charcole/zmachine3270/Firmware/main/libssh2/kex.c

/* Copyright (c) 2004-2007, Sara Golemon <sarag@libssh2.org>
 * Copyright (c) 2010-2019, Daniel Stenberg <daniel@haxx.se>
 * All rights reserved.
 *
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
 *   Redistributions of source code must retain the above
 *   copyright notice, this list of conditions and the
 *   following disclaimer.
 *
 *   Redistributions in binary form must reproduce the above
 *   copyright notice, this list of conditions and the following
 *   disclaimer in the documentation and/or other materials
 *   provided with the distribution.
 *
 *   Neither the name of the copyright holder nor the names
 *   of any other contributors may be used to endorse or
 *   promote products derived from this software without
 *   specific prior written permission.
 *
 * THIS SOFTWARE IS PROVIDED BY THE COPYRIGHT HOLDERS AND
 * CONTRIBUTORS "AS IS" AND ANY EXPRESS OR IMPLIED WARRANTIES,
 * INCLUDING, BUT NOT LIMITED TO, THE IMPLIED WARRANTIES
 * OF MERCHANTABILITY AND FITNESS FOR A PARTICULAR PURPOSE
 * ARE DISCLAIMED. IN NO EVENT SHALL THE COPYRIGHT OWNER OR
 * CONTRIBUTORS BE LIABLE FOR ANY DIRECT, INDIRECT, INCIDENTAL,
 * SPECIAL, EXEMPLARY, OR CONSEQUENTIAL DAMAGES (INCLUDING,
 * BUT NOT LIMITED TO, PROCUREMENT OF SUBSTITUTE GOODS OR
 * SERVICES; LOSS OF USE, DATA, OR PROFITS; OR BUSINESS
 * INTERRUPTION) HOWEVER CAUSED AND ON ANY THEORY OF LIABILITY,
 * WHETHER IN CONTRACT, STRICT LIABILITY, OR TORT (INCLUDING
 * NEGLIGENCE OR OTHERWISE) ARISING IN ANY WAY OUT OF THE
 * USE OF THIS SOFTWARE, EVEN IF ADVISED OF THE POSSIBILITY
 * OF SUCH DAMAGE.
 */

#include "libssh2_priv.h"

#include "transport.h"
#include "comp.h"
#include "mac.h"

/* TODO: Switch this to an inline and handle alloc() failures */
/* Helper macro called from
   kex_method_diffie_hellman_group1_sha1_key_exchange */
#define LIBSSH2_KEX_METHOD_DIFFIE_HELLMAN_SHA1_HASH(value, reqlen, version) \
    {                                                                   \
        libssh2_sha1_ctx hash;                                          \
        unsigned long len = 0;                                          \
        if(!(value)) {                                                  \
            value = LIBSSH2_ALLOC(session, reqlen + SHA_DIGEST_LENGTH); \
        }                                                               \
        if(value)                                                       \
            while(len < (unsigned long)reqlen) {                        \
                libssh2_sha1_init(&hash);                               \
                libssh2_sha1_update(hash, exchange_state->k_value,      \
                                    exchange_state->k_value_len);       \
                libssh2_sha1_update(hash, exchange_state->h_sig_comp,   \
                                    SHA_DIGEST_LENGTH);                 \
                if(len > 0) {                                           \
                    libssh2_sha1_update(hash, value, len);              \
                }                                                       \
                else {                                                  \
                    libssh2_sha1_update(hash, (version), 1);            \
                    libssh2_sha1_update(hash, session->session_id,      \
                                        session->session_id_len);       \
                }                                                       \
                libssh2_sha1_final(hash, (value) + len);                \
                len += SHA_DIGEST_LENGTH;                               \
            }                                                           \
    }                                                                   \


#define LIBSSH2_KEX_METHOD_EC_SHA_VALUE_HASH(value, reqlen, version)    \
    {                                                                   \
        if(type == LIBSSH2_EC_CURVE_NISTP256) {                         \
            LIBSSH2_KEX_METHOD_SHA_VALUE_HASH(256, value, reqlen, version); \
        }                                                               \
        else if(type == LIBSSH2_EC_CURVE_NISTP384) {                    \
            LIBSSH2_KEX_METHOD_SHA_VALUE_HASH(384, value, reqlen, version); \
        }                                                               \
        else if(type == LIBSSH2_EC_CURVE_NISTP521) {                    \
            LIBSSH2_KEX_METHOD_SHA_VALUE_HASH(512, value, reqlen, version); \
        }                                                               \
    }                                                                   \


#define LIBSSH2_KEX_METHOD_SHA_VALUE_HASH(digest_type, value,           \
                                          reqlen, version)              \
{                                                                       \
    libssh2_sha##digest_type##_ctx hash;                                \
    unsigned long len = 0;                                              \
    if(!(value)) {                                                      \
        value = LIBSSH2_ALLOC(session,                                  \
                              reqlen + SHA##digest_type##_DIGEST_LENGTH); \
    }                                                                   \
    if(value)                                                           \
        while(len < (unsigned long)reqlen) {                            \
            libssh2_sha##digest_type##_init(&hash);                     \
            libssh2_sha##digest_type##_update(hash,                     \
                                              exchange_state->k_value,  \
                                              exchange_state->k_value_len); \
            libssh2_sha##digest_type##_update(hash,                     \
                                              exchange_state->h_sig_comp, \
                                         SHA##digest_type##_DIGEST_LENGTH); \
            if(len > 0) {                                               \
                libssh2_sha##digest_type##_update(hash, value, len);    \
            }                                                           \
            else {                                                      \
                libssh2_sha##digest_type##_update(hash, (version), 1);  \
                libssh2_sha##digest_type##_update(hash, session->session_id, \
                                                  session->session_id_len); \
            }                                                           \
            libssh2_sha##digest_type##_final(hash, (value) + len);      \
            len += SHA##digest_type##_DIGEST_LENGTH;                    \
        }                                                               \
}


/*
 * diffie_hellman_sha1
 *
 * Diffie Hellman Key Exchange, Group Agnostic
 */
static int diffie_hellman_sha1(LIBSSH2_SESSION *session,
                               _libssh2_bn *g,
                               _libssh2_bn *p,
                               int group_order,
                               unsigned char packet_type_init,
                               unsigned char packet_type_reply,
                               unsigned char *midhash,
                               unsigned long midhash_len,
                               kmdhgGPshakex_state_t *exchange_state)
{
    int ret = 0;
    int rc;
    libssh2_sha1_ctx exchange_hash_ctx;

    if(exchange_state->state == libssh2_NB_state_idle) {
        /* Setup initial values */
        exchange_state->e_packet = NULL;
        exchange_state->s_packet = NULL;
        exchange_state->k_value = NULL;
        exchange_state->ctx = _libssh2_bn_ctx_new();
        libssh2_dh_init(&exchange_state->x);
        exchange_state->e = _libssh2_bn_init(); /* g^x mod p */
        exchange_state->f = _libssh2_bn_init_from_bin(); /* g^(Random from
                                                            server) mod p */
        exchange_state->k = _libssh2_bn_init(); /* The shared secret: f^x mod
                                                   p */

        /* Zero the whole thing out */
        memset(&exchange_state->req_state, 0, sizeof(packet_require_state_t));

        /* Generate x and e */
        rc = libssh2_dh_key_pair(&exchange_state->x, exchange_state->e, g, p,
                                 group_order, exchange_state->ctx);
        if(rc)
            goto clean_exit;

        /* Send KEX init */
        /* packet_type(1) + String Length(4) + leading 0(1) */
        exchange_state->e_packet_len =
            _libssh2_bn_bytes(exchange_state->e) + 6;
        if(_libssh2_bn_bits(exchange_state->e) % 8) {
            /* Leading 00 not needed */
            exchange_state->e_packet_len--;
        }

        exchange_state->e_packet =
            LIBSSH2_ALLOC(session, exchange_state->e_packet_len);
        if(!exchange_state->e_packet) {
            ret = _libssh2_error(session, LIBSSH2_ERROR_ALLOC,
                                 "Out of memory error");
            goto clean_exit;
        }
        exchange_state->e_packet[0] = packet_type_init;
        _libssh2_htonu32(exchange_state->e_packet + 1,
                         exchange_state->e_packet_len - 5);
        if(_libssh2_bn_bits(exchange_state->e) % 8) {
            _libssh2_bn_to_bin(exchange_state->e,
                               exchange_state->e_packet + 5);
        }
        else {
            exchange_state->e_packet[5] = 0;
            _libssh2_bn_to_bin(exchange_state->e,
                               exchange_state->e_packet + 6);
        }

        _libssh2_debug(session, LIBSSH2_TRACE_KEX, "Sending KEX packet %d",
                       (int) packet_type_init);
        exchange_state->state = libssh2_NB_state_created;
    }

    if(exchange_state->state == libssh2_NB_state_created) {
        rc = _libssh2_transport_send(session, exchange_state->e_packet,
                                     exchange_state->e_packet_len,
                                     NULL, 0);
        if(rc == LIBSSH2_ERROR_EAGAIN) {
            return rc;
        }
        else if(rc) {
            ret = _libssh2_error(session, rc,
                                 "Unable to send KEX init message");
            goto clean_exit;
        }
        exchange_state->state = libssh2_NB_state_sent;
    }

    if(exchange_state->state == libssh2_NB_state_sent) {
        if(session->burn_optimistic_kexinit) {
            /* The first KEX packet to come along will be the guess initially
             * sent by the server.  That guess turned out to be wrong so we
             * need to silently ignore it */
            int burn_type;

            _libssh2_debug(session, LIBSSH2_TRACE_KEX,
                           "Waiting for badly guessed KEX packet "
                           "(to be ignored)");
            burn_type =
                _libssh2_packet_burn(session, &exchange_state->burn_state);
            if(burn_type == LIBSSH2_ERROR_EAGAIN) {
                return burn_type;
            }
            else if(burn_type <= 0) {
                /* Failed to receive a packet */
                ret = burn_type;
                goto clean_exit;
            }
            session->burn_optimistic_kexinit = 0;

            _libssh2_debug(session, LIBSSH2_TRACE_KEX,
                           "Burnt packet of type: %02x",
                           (unsigned int) burn_type);
        }

        exchange_state->state = libssh2_NB_state_sent1;
    }

    if(exchange_state->state == libssh2_NB_state_sent1) {
        /* Wait for KEX reply */
        struct string_buf buf;
        size_t host_key_len;

        rc = _libssh2_packet_require(session, packet_type_reply,
                                     &exchange_state->s_packet,
                                     &exchange_state->s_packet_len, 0, NULL,
                                     0, &exchange_state->req_state);
        if(rc == LIBSSH2_ERROR_EAGAIN) {
            return rc;
        }
        if(rc) {
            ret = _libssh2_error(session, LIBSSH2_ERROR_TIMEOUT,
                                 "Timed out waiting for KEX reply");
            goto clean_exit;
        }

        /* Parse KEXDH_REPLY */
        if(exchange_state->s_packet_len < 5) {
            ret = _libssh2_error(session, LIBSSH2_ERROR_PROTO,
                                 "Unexpected packet length");
            goto clean_exit;
        }

        buf.data = exchange_state->s_packet;
        buf.len = exchange_state->s_packet_len;
        buf.dataptr = buf.data;
        buf.dataptr++; /* advance past type */

        if(session->server_hostkey)
            LIBSSH2_FREE(session, session->server_hostkey);

        if(_libssh2_copy_string(session, &buf, &(session->server_hostkey),
                                &host_key_len)) {
            ret = _libssh2_error(session, LIBSSH2_ERROR_ALLOC,
                                 "Could not copy host key");
            goto clean_exit;
        }

        session->server_hostkey_len = (uint32_t)host_key_len;

#if LIBSSH2_MD5
        {
            libssh2_md5_ctx fingerprint_ctx;

            if(libssh2_md5_init(&fingerprint_ctx)) {
                libssh2_md5_update(fingerprint_ctx, session->server_hostkey,
                                   session->server_hostkey_len);
                libssh2_md5_final(fingerprint_ctx,
                                  session->server_hostkey_md5);
                session->server_hostkey_md5_valid = TRUE;
            }
            else {
                session->server_hostkey_md5_valid = FALSE;
            }
        }
#ifdef LIBSSH2DEBUG
        {
            char fingerprint[50], *fprint = fingerprint;
            int i;
            for(i = 0; i < 16; i++, fprint += 3) {
                snprintf(fprint, 4, "%02x:", session->server_hostkey_md5[i]);
            }
            *(--fprint) = '\0';
            _libssh2_debug(session, LIBSSH2_TRACE_KEX,
                           "Server's MD5 Fingerprint: %s", fingerprint);
        }
#endif /* LIBSSH2DEBUG */
#endif /* ! LIBSSH2_MD5 */

        {
            libssh2_sha1_ctx fingerprint_ctx;

            if(libssh2_sha1_init(&fingerprint_ctx)) {
                libssh2_sha1_update(fingerprint_ctx, session->server_hostkey,
                                    session->server_hostkey_len);
                libssh2_sha1_final(fingerprint_ctx,
                                   session->server_hostkey_sha1);
                session->server_hostkey_sha1_valid = TRUE;
            }
            else {
                session->server_hostkey_sha1_valid = FALSE;
            }
        }
#ifdef LIBSSH2DEBUG
        {
            char fingerprint[64], *fprint = fingerprint;
            int i;

            for(i = 0; i < 20; i++, fprint += 3) {
                snprintf(fprint, 4, "%02x:", session->server_hostkey_sha1[i]);
            }
            *(--fprint) = '\0';
            _libssh2_debug(session, LIBSSH2_TRACE_KEX,
                           "Server's SHA1 Fingerprint: %s", fingerprint);
        }
#endif /* LIBSSH2DEBUG */

        {
            libssh2_sha256_ctx fingerprint_ctx;

            if(libssh2_sha256_init(&fingerprint_ctx)) {
                libssh2_sha256_update(fingerprint_ctx, session->server_hostkey,
                                    session->server_hostkey_len);
                libssh2_sha256_final(fingerprint_ctx,
                                   session->server_hostkey_sha256);
                session->server_hostkey_sha256_valid = TRUE;
            }
            else {
                session->server_hostkey_sha256_valid = FALSE;
            }
        }
#ifdef LIBSSH2DEBUG
        {
            char *base64Fingerprint = NULL;
            _libssh2_base64_encode(session,
                                   (const char *)
                                   session->server_hostkey_sha256,
                                   SHA256_DIGEST_LENGTH, &base64Fingerprint);
            if(base64Fingerprint != NULL) {
                _libssh2_debug(session, LIBSSH2_TRACE_KEX,
                               "Server's SHA256 Fingerprint: %s",
                               base64Fingerprint);
                LIBSSH2_FREE(session, base64Fingerprint);
            }
        }
#endif /* LIBSSH2DEBUG */


        if(session->hostkey->init(session, session->server_hostkey,
                                   session->server_hostkey_len,
                                   &session->server_hostkey_abstract)) {
            ret = _libssh2_error(session, LIBSSH2_ERROR_HOSTKEY_INIT,
                                 "Unable to initialize hostkey importer");
            goto clean_exit;
        }

        if(_libssh2_get_string(&buf, &(exchange_state->f_value),
                               &(exchange_state->f_value_len))) {
            ret = _libssh2_error(session, LIBSSH2_ERROR_HOSTKEY_INIT,
                                 "Unable to get f value");
            goto clean_exit;
        }

        _libssh2_bn_from_bin(exchange_state->f, exchange_state->f_value_len,
                             exchange_state->f_value);

        if(_libssh2_get_string(&buf, &(exchange_state->h_sig),
                               &(exchange_state->h_sig_len))) {
            ret = _libssh2_error(session, LIBSSH2_ERROR_HOSTKEY_INIT,
                                 "Unable to get h sig");
            goto clean_exit;
        }

        /* Compute the shared secret */
        libssh2_dh_secret(&exchange_state->x, exchange_state->k,
                          exchange_state->f, p, exchange_state->ctx);
        exchange_state->k_value_len = _libssh2_bn_bytes(exchange_state->k) + 5;
        if(_libssh2_bn_bits(exchange_state->k) % 8) {
            /* don't need leading 00 */
            exchange_state->k_value_len--;
        }
        exchange_state->k_value =
            LIBSSH2_ALLOC(session, exchange_state->k_value_len);
        if(!exchange_state->k_value) {
            ret = _libssh2_error(session, LIBSSH2_ERROR_ALLOC,
                                 "Unable to allocate buffer for K");
            goto clean_exit;
        }
        _libssh2_htonu32(exchange_state->k_value,
                         exchange_state->k_value_len - 4);
        if(_libssh2_bn_bits(exchange_state->k) % 8) {
            _libssh2_bn_to_bin(exchange_state->k, exchange_state->k_value + 4);
        }
        else {
            exchange_state->k_value[4] = 0;
            _libssh2_bn_to_bin(exchange_state->k, exchange_state->k_value + 5);
        }

        exchange_state->exchange_hash = (void *)&exchange_hash_ctx;
        libssh2_sha1_init(&exchange_hash_ctx);

        if(session->local.banner) {
            _libssh2_htonu32(exchange_state->h_sig_comp,
                             strlen((char *) session->local.banner) - 2);
            libssh2_sha1_update(exchange_hash_ctx,
                                exchange_state->h_sig_comp, 4);
            libssh2_sha1_update(exchange_hash_ctx,
                                session->local.banner,
                                strlen((char *) session->local.banner) - 2);
        }
        else {
            _libssh2_htonu32(exchange_state->h_sig_comp,
                             sizeof(LIBSSH2_SSH_DEFAULT_BANNER) - 1);
            libssh2_sha1_update(exchange_hash_ctx,
                                exchange_state->h_sig_comp, 4);
            libssh2_sha1_update(exchange_hash_ctx,
                                (const unsigned char *)
                                LIBSSH2_SSH_DEFAULT_BANNER,
                                sizeof(LIBSSH2_SSH_DEFAULT_BANNER) - 1);
        }

        _libssh2_htonu32(exchange_state->h_sig_comp,
                         strlen((char *) session->remote.banner));
        libssh2_sha1_update(exchange_hash_ctx,
                            exchange_state->h_sig_comp, 4);
        libssh2_sha1_update(exchange_hash_ctx,
                            session->remote.banner,
                            strlen((char *) session->remote.banner));

        _libssh2_htonu32(exchange_state->h_sig_comp,
                         session->local.kexinit_len);
        libssh2_sha1_update(exchange_hash_ctx,
                            exchange_state->h_sig_comp, 4);
        libssh2_sha1_update(exchange_hash_ctx,
                            session->local.kexinit,
                            session->local.kexinit_len);

        _libssh2_htonu32(exchange_state->h_sig_comp,
                         session->remote.kexinit_len);
        libssh2_sha1_update(exchange_hash_ctx,
                            exchange_state->h_sig_comp, 4);
        libssh2_sha1_update(exchange_hash_ctx,
                            session->remote.kexinit,
                            session->remote.kexinit_len);

        _libssh2_htonu32(exchange_state->h_sig_comp,
                         session->server_hostkey_len);
        libssh2_sha1_update(exchange_hash_ctx,
                            exchange_state->h_sig_comp, 4);
        libssh2_sha1_update(exchange_hash_ctx,
                            session->server_hostkey,
                            session->server_hostkey_len);

        if(packet_type_init == SSH_MSG_KEX_DH_GEX_INIT) {
            /* diffie-hellman-group-exchange hashes additional fields */
#ifdef LIBSSH2_DH_GEX_NEW
            _libssh2_htonu32(exchange_state->h_sig_comp,
                             LIBSSH2_DH_GEX_MINGROUP);
            _libssh2_htonu32(exchange_state->h_sig_comp + 4,
                             LIBSSH2_DH_GEX_OPTGROUP);
            _libssh2_htonu32(exchange_state->h_sig_comp + 8,
                             LIBSSH2_DH_GEX_MAXGROUP);
            libssh2_sha1_update(exchange_hash_ctx,
                                exchange_state->h_sig_comp, 12);
#else
            _libssh2_htonu32(exchange_state->h_sig_comp,
                             LIBSSH2_DH_GEX_OPTGROUP);
            libssh2_sha1_update(exchange_hash_ctx,
                                exchange_state->h_sig_comp, 4);
#endif
        }

        if(midhash) {
            libssh2_sha1_update(exchange_hash_ctx, midhash,
                                midhash_len);
        }

        libssh2_sha1_update(exchange_hash_ctx,
                            exchange_state->e_packet + 1,
                            exchange_state->e_packet_len - 1);

        _libssh2_htonu32(exchange_state->h_sig_comp,
                         exchange_state->f_value_len);
        libssh2_sha1_update(exchange_hash_ctx,
                            exchange_state->h_sig_comp, 4);
        libssh2_sha1_update(exchange_hash_ctx,
                            exchange_state->f_value,
                            exchange_state->f_value_len);

        libssh2_sha1_update(exchange_hash_ctx,
                            exchange_state->k_value,
                            exchange_state->k_value_len);

        libssh2_sha1_final(exchange_hash_ctx,
                           exchange_state->h_sig_comp);

        if(session->hostkey->
            sig_verify(session, exchange_state->h_sig,
                       exchange_state->h_sig_len, exchange_state->h_sig_comp,
                       20, &session->server_hostkey_abstract)) {
            ret = _libssh2_error(session, LIBSSH2_ERROR_HOSTKEY_SIGN,
                                 "Unable to verify hostkey signature");
            goto clean_exit;
        }

        _libssh2_debug(session, LIBSSH2_TRACE_KEX, "Sending NEWKEYS message");
        exchange_state->c = SSH_MSG_NEWKEYS;

        exchange_state->state = libssh2_NB_state_sent2;
    }

    if(exchange_state->state == libssh2_NB_state_sent2) {
        rc = _libssh2_transport_send(session, &exchange_state->c, 1, NULL, 0);
        if(rc == LIBSSH2_ERROR_EAGAIN) {
            return rc;
        }
        else if(rc) {
            ret = _libssh2_error(session, rc,
                                 "Unable to send NEWKEYS message");
            goto clean_exit;
        }

        exchange_state->state = libssh2_NB_state_sent3;
    }

    if(exchange_state->state == libssh2_NB_state_sent3) {
        rc = _libssh2_packet_require(session, SSH_MSG_NEWKEYS,
                                     &exchange_state->tmp,
                                     &exchange_state->tmp_len, 0, NULL, 0,
                                     &exchange_state->req_state);
        if(rc == LIBSSH2_ERROR_EAGAIN) {
            return rc;
        }
        else if(rc) {
            ret = _libssh2_error(session, rc, "Timed out waiting for NEWKEYS");
            goto clean_exit;
        }
        /* The first key exchange has been performed,
           switch to active crypt/comp/mac mode */
        session->state |= LIBSSH2_STATE_NEWKEYS;
        _libssh2_debug(session, LIBSSH2_TRACE_KEX, "Received NEWKEYS message");

        /* This will actually end up being just packet_type(1)
           for this packet type anyway */
        LIBSSH2_FREE(session, exchange_state->tmp);

        if(!session->session_id) {
            session->session_id = LIBSSH2_ALLOC(session, SHA_DIGEST_LENGTH);
            if(!session->session_id) {
                ret = _libssh2_error(session, LIBSSH2_ERROR_ALLOC,
                                     "Unable to allocate buffer for "
                                     "SHA digest");
                goto clean_exit;
            }
            memcpy(session->session_id, exchange_state->h_sig_comp,
                   SHA_DIGEST_LENGTH);
            session->session_id_len = SHA_DIGEST_LENGTH;
            _libssh2_debug(session, LIBSSH2_TRACE_KEX,
                           "session_id calculated");
        }

        /* Cleanup any existing cipher */
        if(session->local.crypt->dtor) {
            session->local.crypt->dtor(session,
                                       &session->local.crypt_abstract);
        }

        /* Calculate IV/Secret/Key for each direction */
        if(session->local.crypt->init) {
            unsigned char *iv = NULL, *secret = NULL;
            int free_iv = 0, free_secret = 0;

            LIBSSH2_KEX_METHOD_DIFFIE_HELLMAN_SHA1_HASH(iv,
                                                        session->local.crypt->
                                                        iv_len,
                                                        (const unsigned char *)
                                                        "A");
            if(!iv) {
                ret = -1;
                goto clean_exit;
            }
            LIBSSH2_KEX_METHOD_DIFFIE_HELLMAN_SHA1_HASH(secret,
                                                        session->local.crypt->
                                                        secret_len,
                                                        (const unsigned char *)
                                                        "C");
            if(!secret) {
                LIBSSH2_FREE(session, iv);
                ret = LIBSSH2_ERROR_KEX_FAILURE;
                goto clean_exit;
            }
            if(session->local.crypt->
                init(session, session->local.crypt, iv, &free_iv, secret,
                     &free_secret, 1, &session->local.crypt_abstract)) {
                LIBSSH2_FREE(session, iv);
                LIBSSH2_FREE(session, secret);
                ret = LIBSSH2_ERROR_KEX_FAILURE;
                goto clean_exit;
            }

            if(free_iv) {
                _libssh2_explicit_zero(iv, session->local.crypt->iv_len);
                LIBSSH2_FREE(session, iv);
            }

            if(free_secret) {
                _libssh2_explicit_zero(secret,
                                       session->local.crypt->secret_len);
                LIBSSH2_FREE(session, secret);
            }
        }
        _libssh2_debug(session, LIBSSH2_TRACE_KEX,
                       "Client to Server IV and Key calculated");

        if(session->remote.crypt->dtor) {
            /* Cleanup any existing cipher */
            session->remote.crypt->dtor(session,
                                        &session->remote.crypt_abstract);
        }

        if(session->remote.crypt->init) {
            unsigned char *iv = NULL, *secret = NULL;
            int free_iv = 0, free_secret = 0;

            LIBSSH2_KEX_METHOD_DIFFIE_HELLMAN_SHA1_HASH(iv,
                                                        session->remote.crypt->
                                                        iv_len,
                                                        (const unsigned char *)
                                                        "B");
            if(!iv) {
                ret = LIBSSH2_ERROR_KEX_FAILURE;
                goto clean_exit;
            }
            LIBSSH2_KEX_METHOD_DIFFIE_HELLMAN_SHA1_HASH(secret,
                                                        session->remote.crypt->
                                                        secret_len,
                                                        (const unsigned char *)
                                                        "D");
            if(!secret) {
                LIBSSH2_FREE(session, iv);
                ret = LIBSSH2_ERROR_KEX_FAILURE;
                goto clean_exit;
            }
            if(session->remote.crypt->
                init(session, session->remote.crypt, iv, &free_iv, secret,
                     &free_secret, 0, &session->remote.crypt_abstract)) {
                LIBSSH2_FREE(session, iv);
                LIBSSH2_FREE(session, secret);
                ret = LIBSSH2_ERROR_KEX_FAILURE;
                goto clean_exit;
            }

            if(free_iv) {
                _libssh2_explicit_zero(iv, session->remote.crypt->iv_len);
                LIBSSH2_FREE(session, iv);
            }

            if(free_secret) {
                _libssh2_explicit_zero(secret,
                                       session->remote.crypt->secret_len);
                LIBSSH2_FREE(session, secret);
            }
        }
        _libssh2_debug(session, LIBSSH2_TRACE_KEX,
                       "Server to Client IV and Key calculated");

        if(session->local.mac->dtor) {
            session->local.mac->dtor(session, &session->local.mac_abstract);
        }

        if(session->local.mac->init) {
            unsigned char *key = NULL;
            int free_key = 0;

            LIBSSH2_KEX_METHOD_DIFFIE_HELLMAN_SHA1_HASH(key,
                                                        session->local.mac->
                                                        key_len,
                                                        (const unsigned char *)
                                                        "E");
            if(!key) {
                ret = LIBSSH2_ERROR_KEX_FAILURE;
                goto clean_exit;
            }
            session->local.mac->init(session, key, &free_key,
                                     &session->local.mac_abstract);

            if(free_key) {
                _libssh2_explicit_zero(key, session->local.mac->key_len);
                LIBSSH2_FREE(session, key);
            }
        }
        _libssh2_debug(session, LIBSSH2_TRACE_KEX,
                       "Client to Server HMAC Key calculated");

        if(session->remote.mac->dtor) {
            session->remote.mac->dtor(session, &session->remote.mac_abstract);
        }

        if(session->remote.mac->init) {
            unsigned char *key = NULL;
            int free_key = 0;

            LIBSSH2_KEX_METHOD_DIFFIE_HELLMAN_SHA1_HASH(key,
                                                        session->remote.mac->
                                                        key_len,
                                                        (const unsigned char *)
                                                        "F");
            if(!key) {
                ret = LIBSSH2_ERROR_KEX_FAILURE;
                goto clean_exit;
            }
            session->remote.mac->init(session, key, &free_key,
                                      &session->remote.mac_abstract);

            if(free_key) {
                _libssh2_explicit_zero(key, session->remote.mac->key_len);
                LIBSSH2_FREE(session, key);
            }
        }
        _libssh2_debug(session, LIBSSH2_TRACE_KEX,
                       "Server to Client HMAC Key calculated");

        /* Initialize compression for each direction */

        /* Cleanup any existing compression */
        if(session->local.comp && session->local.comp->dtor) {
            session->local.comp->dtor(session, 1,
                                      &session->local.comp_abstract);
        }

        if(session->local.comp && session->local.comp->init) {
            if(session->local.comp->init(session, 1,
                                          &session->local.comp_abstract)) {
                ret = LIBSSH2_ERROR_KEX_FAILURE;
                goto clean_exit;
            }
        }
        _libssh2_debug(session, LIBSSH2_TRACE_KEX,
                       "Client to Server compression initialized");

        if(session->remote.comp && session->remote.comp->dtor) {
            session->remote.comp->dtor(session, 0,
                                       &session->remote.comp_abstract);
        }

        if(session->remote.comp && session->remote.comp->init) {
            if(session->remote.comp->init(session, 0,
                                           &session->remote.comp_abstract)) {
                ret = LIBSSH2_ERROR_KEX_FAILURE;
                goto clean_exit;
            }
        }
        _libssh2_debug(session, LIBSSH2_TRACE_KEX,
                       "Server to Client compression initialized");

    }

  clean_exit:
    libssh2_dh_dtor(&exchange_state->x);
    _libssh2_bn_free(exchange_state->e);
    exchange_state->e = NULL;
    _libssh2_bn_free(exchange_state->f);
    exchange_state->f = NULL;
    _libssh2_bn_free(exchange_state->k);
    exchange_state->k = NULL;
    _libssh2_bn_ctx_free(exchange_state->ctx);
    exchange_state->ctx = NULL;

    if(exchange_state->e_packet) {
        LIBSSH2_FREE(session, exchange_state->e_packet);
        exchange_state->e_packet = NULL;
    }

    if(exchange_state->s_packet) {
        LIBSSH2_FREE(session, exchange_state->s_packet);
        exchange_state->s_packet = NULL;
    }

    if(exchange_state->k_value) {
        LIBSSH2_FREE(session, exchange_state->k_value);
        exchange_state->k_value = NULL;
    }

    exchange_state->state = libssh2_NB_state_idle;

    return ret;
}


/*
 * diffie_hellman_sha256
 *
 * Diffie Hellman Key Exchange, Group Agnostic
 */
static int diffie_hellman_sha256(LIBSSH2_SESSION *session,
                                 _libssh2_bn *g,
                                 _libssh2_bn *p,
                                 int group_order,
                                 unsigned char packet_type_init,
                                 unsigned char packet_type_reply,
                                 unsigned char *midhash,
                                 unsigned long midhash_len,
                                 kmdhgGPshakex_state_t *exchange_state)
{
    int ret = 0;
    int rc;
    libssh2_sha256_ctx exchange_hash_ctx;

    if(exchange_state->state == libssh2_NB_state_idle) {
        /* Setup initial values */
        exchange_state->e_packet = NULL;
        exchange_state->s_packet = NULL;
        exchange_state->k_value = NULL;
        exchange_state->ctx = _libssh2_bn_ctx_new();
        libssh2_dh_init(&exchange_state->x);
        exchange_state->e = _libssh2_bn_init(); /* g^x mod p */
        exchange_state->f = _libssh2_bn_init_from_bin(); /* g^(Random from
                                                            server) mod p */
        exchange_state->k = _libssh2_bn_init(); /* The shared secret: f^x mod
                                                   p */

        /* Zero the whole thing out */
        memset(&exchange_state->req_state, 0, sizeof(packet_require_state_t));

        /* Generate x and e */
        rc = libssh2_dh_key_pair(&exchange_state->x, exchange_state->e, g, p,
                                 group_order, exchange_state->ctx);
        if(rc)
            goto clean_exit;

        /* Send KEX init */
        /* packet_type(1) + String Length(4) + leading 0(1) */
        exchange_state->e_packet_len =
            _libssh2_bn_bytes(exchange_state->e) + 6;
        if(_libssh2_bn_bits(exchange_state->e) % 8) {
            /* Leading 00 not needed */
            exchange_state->e_packet_len--;
        }

        exchange_state->e_packet =
            LIBSSH2_ALLOC(session, exchange_state->e_packet_len);
        if(!exchange_state->e_packet) {
            ret = _libssh2_error(session, LIBSSH2_ERROR_ALLOC,
                                 "Out of memory error");
            goto clean_exit;
        }
        exchange_state->e_packet[0] = packet_type_init;
        _libssh2_htonu32(exchange_state->e_packet + 1,
                         exchange_state->e_packet_len - 5);
        if(_libssh2_bn_bits(exchange_state->e) % 8) {
            _libssh2_bn_to_bin(exchange_state->e,
                               exchange_state->e_packet + 5);
        }
        else {
            exchange_state->e_packet[5] = 0;
            _libssh2_bn_to_bin(exchange_state->e,
                               exchange_state->e_packet + 6);
        }

        _libssh2_debug(session, LIBSSH2_TRACE_KEX, "Sending KEX packet %d",
                       (int) packet_type_init);
        exchange_state->state = libssh2_NB_state_created;
    }

    if(exchange_state->state == libssh2_NB_state_created) {
        rc = _libssh2_transport_send(session, exchange_state->e_packet,
                                     exchange_state->e_packet_len,
                                     NULL, 0);
        if(rc == LIBSSH2_ERROR_EAGAIN) {
            return rc;
        }
        else if(rc) {
            ret = _libssh2_error(session, rc,
                                 "Unable to send KEX init message");
            goto clean_exit;
        }
        exchange_state->state = libssh2_NB_state_sent;
    }

    if(exchange_state->state == libssh2_NB_state_sent) {
        if(session->burn_optimistic_kexinit) {
            /* The first KEX packet to come along will be the guess initially
             * sent by the server.  That guess turned out to be wrong so we
             * need to silently ignore it */
            int burn_type;

            _libssh2_debug(session, LIBSSH2_TRACE_KEX,
                           "Waiting for badly guessed KEX packet "
                           "(to be ignored)");
            burn_type =
                _libssh2_packet_burn(session, &exchange_state->burn_state);
            if(burn_type == LIBSSH2_ERROR_EAGAIN) {
                return burn_type;
            }
            else if(burn_type <= 0) {
                /* Failed to receive a packet */
                ret = burn_type;
                goto clean_exit;
            }
            session->burn_optimistic_kexinit = 0;

            _libssh2_debug(session, LIBSSH2_TRACE_KEX,
                           "Burnt packet of type: %02x",
                           (unsigned int) burn_type);
        }

        exchange_state->state = libssh2_NB_state_sent1;
    }

    if(exchange_state->state == libssh2_NB_state_sent1) {
        /* Wait for KEX reply */
        struct string_buf buf;
        size_t host_key_len;

        rc = _libssh2_packet_require(session, packet_type_reply,
                                     &exchange_state->s_packet,
                                     &exchange_state->s_packet_len, 0, NULL,
                                     0, &exchange_state->req_state);
        if(rc == LIBSSH2_ERROR_EAGAIN) {
            return rc;
        }
        if(rc) {
            ret = _libssh2_error(session, LIBSSH2_ERROR_TIMEOUT,
                                 "Timed out waiting for KEX reply");
            goto clean_exit;
        }

        /* Parse KEXDH_REPLY */
        if(exchange_state->s_packet_len < 5) {
            ret = _libssh2_error(session, LIBSSH2_ERROR_PROTO,
                                 "Unexpected packet length");
            goto clean_exit;
        }

        buf.data = exchange_state->s_packet;
        buf.len = exchange_state->s_packet_len;
        buf.dataptr = buf.data;
        buf.dataptr++; /* advance past type */

        if(session->server_hostkey)
            LIBSSH2_FREE(session, session->server_hostkey);

        if(_libssh2_copy_string(session, &buf, &(session->server_hostkey),
                                &host_key_len)) {
            ret = _libssh2_error(session, LIBSSH2_ERROR_ALLOC,
                                 "Could not copy host key");
            goto clean_exit;
        }

        session->server_hostkey_len = (uint32_t)host_key_len;

#if LIBSSH2_MD5
        {
            libssh2_md5_ctx fingerprint_ctx;

            if(libssh2_md5_init(&fingerprint_ctx)) {
                libssh2_md5_update(fingerprint_ctx, session->server_hostkey,
                                   session->server_hostkey_len);
                libssh2_md5_final(fingerprint_ctx,
                                  session->server_hostkey_md5);
                session->server_hostkey_md5_valid = TRUE;
            }
            else {
                session->server_hostkey_md5_valid = FALSE;
            }
        }
#ifdef LIBSSH2DEBUG
        {
            char fingerprint[50], *fprint = fingerprint;
            int i;
            for(i = 0; i < 16; i++, fprint += 3) {
                snprintf(fprint, 4, "%02x:", session->server_hostkey_md5[i]);
            }
            *(--fprint) = '\0';
            _libssh2_debug(session, LIBSSH2_TRACE_KEX,
                           "Server's MD5 Fingerprint: %s", fingerprint);
        }
#endif /* LIBSSH2DEBUG */
#endif /* ! LIBSSH2_MD5 */

        {
            libssh2_sha1_ctx fingerprint_ctx;

            if(libssh2_sha1_init(&fingerprint_ctx)) {
                libssh2_sha1_update(fingerprint_ctx, session->server_hostkey,
                                    session->server_hostkey_len);
                libssh2_sha1_final(fingerprint_ctx,
                                   session->server_hostkey_sha1);
                session->server_hostkey_sha1_valid = TRUE;
            }
            else {
                session->server_hostkey_sha1_valid = FALSE;
            }
        }
#ifdef LIBSSH2DEBUG
        {
            char fingerprint[64], *fprint = fingerprint;
            int i;

            for(i = 0; i < 20; i++, fprint += 3) {
                snprintf(fprint, 4, "%02x:", session->server_hostkey_sha1[i]);
            }
            *(--fprint) = '\0';
            _libssh2_debug(session, LIBSSH2_TRACE_KEX,
                           "Server's SHA1 Fingerprint: %s", fingerprint);
        }
#endif /* LIBSSH2DEBUG */

        {
            libssh2_sha256_ctx fingerprint_ctx;

            if(libssh2_sha256_init(&fingerprint_ctx)) {
                libssh2_sha256_update(fingerprint_ctx, session->server_hostkey,
                                      session->server_hostkey_len);
                libssh2_sha256_final(fingerprint_ctx,
                                     session->server_hostkey_sha256);
                session->server_hostkey_sha256_valid = TRUE;
            }
            else {
                session->server_hostkey_sha256_valid = FALSE;
            }
        }
#ifdef LIBSSH2DEBUG
        {
            char *base64Fingerprint = NULL;
            _libssh2_base64_encode(session,
                                   (const char *)
                                   session->server_hostkey_sha256,
                                   SHA256_DIGEST_LENGTH, &base64Fingerprint);
            if(base64Fingerprint != NULL) {
                _libssh2_debug(session, LIBSSH2_TRACE_KEX,
                               "Server's SHA256 Fingerprint: %s",
                               base64Fingerprint);
                LIBSSH2_FREE(session, base64Fingerprint);
            }
        }
#endif /* LIBSSH2DEBUG */

        if(session->hostkey->init(session, session->server_hostkey,
                                   session->server_hostkey_len,
                                   &session->server_hostkey_abstract)) {
            ret = _libssh2_error(session, LIBSSH2_ERROR_HOSTKEY_INIT,
                                 "Unable to initialize hostkey importer");
            goto clean_exit;
        }

        if(_libssh2_get_string(&buf, &(exchange_state->f_value),
                               &(exchange_state->f_value_len))) {
            ret = _libssh2_error(session, LIBSSH2_ERROR_HOSTKEY_INIT,
                                 "Unable to get f value");
            goto clean_exit;
        }

        _libssh2_bn_from_bin(exchange_state->f, exchange_state->f_value_len,
                             exchange_state->f_value);

        if(_libssh2_get_string(&buf, &(exchange_state->h_sig),
                               &(exchange_state->h_sig_len))) {
            ret = _libssh2_error(session, LIBSSH2_ERROR_HOSTKEY_INIT,
                                 "Unable to get h sig");
            goto clean_exit;
        }

        /* Compute the shared secret */
        libssh2_dh_secret(&exchange_state->x, exchange_state->k,
                          exchange_state->f, p, exchange_state->ctx);
        exchange_state->k_value_len = _libssh2_bn_bytes(exchange_state->k) + 5;
        if(_libssh2_bn_bits(exchange_state->k) % 8) {
            /* don't need leading 00 */
            exchange_state->k_value_len--;
        }
        exchange_state->k_value =
            LIBSSH2_ALLOC(session, exchange_state->k_value_len);
        if(!exchange_state->k_value) {
            ret = _libssh2_error(session, LIBSSH2_ERROR_ALLOC,
                                 "Unable to allocate buffer for K");
            goto clean_exit;
        }
        _libssh2_htonu32(exchange_state->k_value,
                         exchange_state->k_value_len - 4);
        if(_libssh2_bn_bits(exchange_state->k) % 8) {
            _libssh2_bn_to_bin(exchange_state->k, exchange_state->k_value + 4);
        }
        else {
            exchange_state->k_value[4] = 0;
            _libssh2_bn_to_bin(exchange_state->k, exchange_state->k_value + 5);
        }

        exchange_state->exchange_hash = (void *)&exchange_hash_ctx;
        libssh2_sha256_init(&exchange_hash_ctx);

        if(session->local.banner) {
            _libssh2_htonu32(exchange_state->h_sig_comp,
                             strlen((char *) session->local.banner) - 2);
            libssh2_sha256_update(exchange_hash_ctx,
                                  exchange_state->h_sig_comp, 4);
            libssh2_sha256_update(exchange_hash_ctx,
                                  session->local.banner,
                                  strlen((char *) session->local.banner) - 2);
        }
        else {
            _libssh2_htonu32(exchange_state->h_sig_comp,
                             sizeof(LIBSSH2_SSH_DEFAULT_BANNER) - 1);
            libssh2_sha256_update(exchange_hash_ctx,
                                  exchange_state->h_sig_comp, 4);
            libssh2_sha256_update(exchange_hash_ctx,
                                  (const unsigned char *)
                                  LIBSSH2_SSH_DEFAULT_BANNER,
                                  sizeof(LIBSSH2_SSH_DEFAULT_BANNER) - 1);
        }

        _libssh2_htonu32(exchange_state->h_sig_comp,
                         strlen((char *) session->remote.banner));
        libssh2_sha256_update(exchange_hash_ctx,
                              exchange_state->h_sig_comp, 4);
        libssh2_sha256_update(exchange_hash_ctx,
                              session->remote.banner,
                              strlen((char *) session->remote.banner));

        _libssh2_htonu32(exchange_state->h_sig_comp,
                         session->local.kexinit_len);
        libssh2_sha256_update(exchange_hash_ctx,
                              exchange_state->h_sig_comp, 4);
        libssh2_sha256_update(exchange_hash_ctx,
                              session->local.kexinit,
                              session->local.kexinit_len);

        _libssh2_htonu32(exchange_state->h_sig_comp,
                         session->remote.kexinit_len);
        libssh2_sha256_update(exchange_hash_ctx,
                              exchange_state->h_sig_comp, 4);
        libssh2_sha256_update(exchange_hash_ctx,
                              session->remote.kexinit,
                              session->remote.kexinit_len);

        _libssh2_htonu32(exchange_state->h_sig_comp,
                         session->server_hostkey_len);
        libssh2_sha256_update(exchange_hash_ctx,
                              exchange_state->h_sig_comp, 4);
        libssh2_sha256_update(exchange_hash_ctx,
                              session->server_hostkey,
                              session->server_hostkey_len);

        if(packet_type_init == SSH_MSG_KEX_DH_GEX_INIT) {
            /* diffie-hellman-group-exchange hashes additional fields */
#ifdef LIBSSH2_DH_GEX_NEW
            _libssh2_htonu32(exchange_state->h_sig_comp,
                             LIBSSH2_DH_GEX_MINGROUP);
            _libssh2_htonu32(exchange_state->h_sig_comp + 4,
                             LIBSSH2_DH_GEX_OPTGROUP);
            _libssh2_htonu32(exchange_state->h_sig_comp + 8,
                             LIBSSH2_DH_GEX_MAXGROUP);
            libssh2_sha256_update(exchange_hash_ctx,
                                  exchange_state->h_sig_comp, 12);
#else
            _libssh2_htonu32(exchange_state->h_sig_comp,
                             LIBSSH2_DH_GEX_OPTGROUP);
            libssh2_sha256_update(exchange_hash_ctx,
                                  exchange_state->h_sig_comp, 4);
#endif
        }

        if(midhash) {
            libssh2_sha256_update(exchange_hash_ctx, midhash,
                                  midhash_len);
        }

        libssh2_sha256_update(exchange_hash_ctx,
                              exchange_state->e_packet + 1,
                              exchange_state->e_packet_len - 1);

        _libssh2_htonu32(exchange_state->h_sig_comp,
                         exchange_state->f_value_len);
        libssh2_sha256_update(exchange_hash_ctx,
                              exchange_state->h_sig_comp, 4);
        libssh2_sha256_update(exchange_hash_ctx,
                              exchange_state->f_value,
                              exchange_state->f_value_len);

        libssh2_sha256_update(exchange_hash_ctx,
                              exchange_state->k_value,
                              exchange_state->k_value_len);

        libssh2_sha256_final(exchange_hash_ctx,
                             exchange_state->h_sig_comp);

        if(session->hostkey->
           sig_verify(session, exchange_state->h_sig,
                      exchange_state->h_sig_len, exchange_state->h_sig_comp,
                      SHA256_DIGEST_LENGTH,
                      &session->server_hostkey_abstract)) {
            ret = _libssh2_error(session, LIBSSH2_ERROR_HOSTKEY_SIGN,
                                 "Unable to verify hostkey signature");
            goto clean_exit;
        }



        _libssh2_debug(session, LIBSSH2_TRACE_KEX, "Sending NEWKEYS message");
        exchange_state->c = SSH_MSG_NEWKEYS;

        exchange_state->state = libssh2_NB_state_sent2;
    }

    if(exchange_state->state == libssh2_NB_state_sent2) {
        rc = _libssh2_transport_send(session, &exchange_state->c, 1, NULL, 0);
        if(rc == LIBSSH2_ERROR_EAGAIN) {
            return rc;
        }
        else if(rc) {
            ret = _libssh2_error(session, rc,
                                 "Unable to send NEWKEYS message");
            goto clean_exit;
        }

        exchange_state->state = libssh2_NB_state_sent3;
    }

    if(exchange_state->state == libssh2_NB_state_sent3) {
        rc = _libssh2_packet_require(session, SSH_MSG_NEWKEYS,
                                     &exchange_state->tmp,
                                     &exchange_state->tmp_len, 0, NULL, 0,
                                     &exchange_state->req_state);
        if(rc == LIBSSH2_ERROR_EAGAIN) {
            return rc;
        }
        else if(rc) {
            ret = _libssh2_error(session, rc, "Timed out waiting for NEWKEYS");
            goto clean_exit;
        }
        /* The first key exchange has been performed,
           switch to active crypt/comp/mac mode */
        session->state |= LIBSSH2_STATE_NEWKEYS;
        _libssh2_debug(session, LIBSSH2_TRACE_KEX, "Received NEWKEYS message");

        /* This will actually end up being just packet_type(1)
           for this packet type anyway */
        LIBSSH2_FREE(session, exchange_state->tmp);

        if(!session->session_id) {
            session->session_id = LIBSSH2_ALLOC(session, SHA256_DIGEST_LENGTH);
            if(!session->session_id) {
                ret = _libssh2_error(session, LIBSSH2_ERROR_ALLOC,
                                     "Unable to allocate buffer for "
                                     "SHA digest");
                goto clean_exit;
            }
            memcpy(session->session_id, exchange_state->h_sig_comp,
                   SHA256_DIGEST_LENGTH);
            session->session_id_len = SHA256_DIGEST_LENGTH;
            _libssh2_debug(session, LIBSSH2_TRACE_KEX,
                           "session_id calculated");
        }

        /* Cleanup any existing cipher */
        if(session->local.crypt->dtor) {
            session->local.crypt->dtor(session,
                                       &session->local.crypt_abstract);
        }

        /* Calculate IV/Secret/Key for each direction */
        if(session->local.crypt->init) {
            unsigned char *iv = NULL, *secret = NULL;
            int free_iv = 0, free_secret = 0;

            LIBSSH2_KEX_METHOD_SHA_VALUE_HASH(256, iv,
                                              session->local.crypt->
                                              iv_len,
                                              (const unsigned char *)"A");
            if(!iv) {
                ret = -1;
                goto clean_exit;
            }
            LIBSSH2_KEX_METHOD_SHA_VALUE_HASH(256, secret,
                                              session->local.crypt->
                                              secret_len,
                                              (const unsigned char *)"C");
            if(!secret) {
                LIBSSH2_FREE(session, iv);
                ret = LIBSSH2_ERROR_KEX_FAILURE;
                goto clean_exit;
            }
            if(session->local.crypt->
                init(session, session->local.crypt, iv, &free_iv, secret,
                     &free_secret, 1, &session->local.crypt_abstract)) {
                LIBSSH2_FREE(session, iv);
                LIBSSH2_FREE(session, secret);
                ret = LIBSSH2_ERROR_KEX_FAILURE;
                goto clean_exit;
            }

            if(free_iv) {
                _libssh2_explicit_zero(iv, session->local.crypt->iv_len);
                LIBSSH2_FREE(session, iv);
            }

            if(free_secret) {
                _libssh2_explicit_zero(secret,
                                       session->local.crypt->secret_len);
                LIBSSH2_FREE(session, secret);
            }
        }
        _libssh2_debug(session, LIBSSH2_TRACE_KEX,
                       "Client to Server IV and Key calculated");

        if(session->remote.crypt->dtor) {
            /* Cleanup any existing cipher */
            session->remote.crypt->dtor(session,
                                        &session->remote.crypt_abstract);
        }

        if(session->remote.crypt->init) {
            unsigned char *iv = NULL, *secret = NULL;
            int free_iv = 0, free_secret = 0;

            LIBSSH2_KEX_METHOD_SHA_VALUE_HASH(256, iv,
                                              session->remote.crypt->
                                              iv_len,
                                              (const unsigned char *)"B");
            if(!iv) {
                ret = LIBSSH2_ERROR_KEX_FAILURE;
                goto clean_exit;
            }
            LIBSSH2_KEX_METHOD_SHA_VALUE_HASH(256, secret,
                                              session->remote.crypt->
                                              secret_len,
                                              (const unsigned char *)"D");
            if(!secret) {
                LIBSSH2_FREE(session, iv);
                ret = LIBSSH2_ERROR_KEX_FAILURE;
                goto clean_exit;
            }
            if(session->remote.crypt->
                init(session, session->remote.crypt, iv, &free_iv, secret,
                     &free_secret, 0, &session->remote.crypt_abstract)) {
                LIBSSH2_FREE(session, iv);
                LIBSSH2_FREE(session, secret);
                ret = LIBSSH2_ERROR_KEX_FAILURE;
                goto clean_exit;
            }

            if(free_iv) {
                _libssh2_explicit_zero(iv, session->remote.crypt->iv_len);
                LIBSSH2_FREE(session, iv);
            }

            if(free_secret) {
                _libssh2_explicit_zero(secret,
                                       session->remote.crypt->secret_len);
                LIBSSH2_FREE(session, secret);
            }
        }
        _libssh2_debug(session, LIBSSH2_TRACE_KEX,
                       "Server to Client IV and Key calculated");

        if(session->local.mac->dtor) {
            session->local.mac->dtor(session, &session->local.mac_abstract);
        }

        if(session->local.mac->init) {
            unsigned char *key = NULL;
            int free_key = 0;

            LIBSSH2_KEX_METHOD_SHA_VALUE_HASH(256, key,
                                              session->local.mac->
                                              key_len,
                                              (const unsigned char *)"E");
            if(!key) {
                ret = LIBSSH2_ERROR_KEX_FAILURE;
                goto clean_exit;
            }
            session->local.mac->init(session, key, &free_key,
                                     &session->local.mac_abstract);

            if(free_key) {
                _libssh2_explicit_zero(key, session->local.mac->key_len);
                LIBSSH2_FREE(session, key);
            }
        }
        _libssh2_debug(session, LIBSSH2_TRACE_KEX,
                       "Client to Server HMAC Key calculated");

        if(session->remote.mac->dtor) {
            session->remote.mac->dtor(session, &session->remote.mac_abstract);
        }

        if(session->remote.mac->init) {
            unsigned char *key = NULL;
            int free_key = 0;

            LIBSSH2_KEX_METHOD_SHA_VALUE_HASH(256, key,
                                              session->remote.mac->
                                              key_len,
                                              (const unsigned char *)"F");
            if(!key) {
                ret = LIBSSH2_ERROR_KEX_FAILURE;
                goto clean_exit;
            }
            session->remote.mac->init(session, key, &free_key,
                                      &session->remote.mac_abstract);

            if(free_key) {
                _libssh2_explicit_zero(key, session->remote.mac->key_len);
                LIBSSH2_FREE(session, key);
            }
        }
        _libssh2_debug(session, LIBSSH2_TRACE_KEX,
                       "Server to Client HMAC Key calculated");

        /* Initialize compression for each direction */

        /* Cleanup any existing compression */
        if(session->local.comp && session->local.comp->dtor) {
            session->local.comp->dtor(session, 1,
                                      &session->local.comp_abstract);
        }

        if(session->local.comp && session->local.comp->init) {
            if(session->local.comp->init(session, 1,
                                          &session->local.comp_abstract)) {
                ret = LIBSSH2_ERROR_KEX_FAILURE;
                goto clean_exit;
            }
        }
        _libssh2_debug(session, LIBSSH2_TRACE_KEX,
                       "Client to Server compression initialized");

        if(session->remote.comp && session->remote.comp->dtor) {
            session->remote.comp->dtor(session, 0,
                                       &session->remote.comp_abstract);
        }

        if(session->remote.comp && session->remote.comp->init) {
            if(session->remote.comp->init(session, 0,
                                           &session->remote.comp_abstract)) {
                ret = LIBSSH2_ERROR_KEX_FAILURE;
                goto clean_exit;
            }
        }
        _libssh2_debug(session, LIBSSH2_TRACE_KEX,
                       "Server to Client compression initialized");

    }

  clean_exit:
    libssh2_dh_dtor(&exchange_state->x);
    _libssh2_bn_free(exchange_state->e);
    exchange_state->e = NULL;
    _libssh2_bn_free(exchange_state->f);
    exchange_state->f = NULL;
    _libssh2_bn_free(exchange_state->k);
    exchange_state->k = NULL;
    _libssh2_bn_ctx_free(exchange_state->ctx);
    exchange_state->ctx = NULL;

    if(exchange_state->e_packet) {
        LIBSSH2_FREE(session, exchange_state->e_packet);
        exchange_state->e_packet = NULL;
    }

    if(exchange_state->s_packet) {
        LIBSSH2_FREE(session, exchange_state->s_packet);
        exchange_state->s_packet = NULL;
    }

    if(exchange_state->k_value) {
        LIBSSH2_FREE(session, exchange_state->k_value);
        exchange_state->k_value = NULL;
    }

    exchange_state->state = libssh2_NB_state_idle;

    return ret;
}



/* kex_method_diffie_hellman_group1_sha1_key_exchange
 * Diffie-Hellman Group1 (Actually Group2) Key Exchange using SHA1
 */
static int
kex_method_diffie_hellman_group1_sha1_key_exchange(LIBSSH2_SESSION *session,
                                                   key_exchange_state_low_t
                                                   * key_state)
{
    static const unsigned char p_value[128] = {
        0xFF, 0xFF, 0xFF, 0xFF, 0xFF, 0xFF, 0xFF, 0xFF,
        0xC9, 0x0F, 0xDA, 0xA2, 0x21, 0x68, 0xC2, 0x34,
        0xC4, 0xC6, 0x62, 0x8B, 0x80, 0xDC, 0x1C, 0xD1,
        0x29, 0x02, 0x4E, 0x08, 0x8A, 0x67, 0xCC, 0x74,
        0x02, 0x0B, 0xBE, 0xA6, 0x3B, 0x13, 0x9B, 0x22,
        0x51, 0x4A, 0x08, 0x79, 0x8E, 0x34, 0x04, 0xDD,
        0xEF, 0x95, 0x19, 0xB3, 0xCD, 0x3A, 0x43, 0x1B,
        0x30, 0x2B, 0x0A, 0x6D, 0xF2, 0x5F, 0x14, 0x37,
        0x4F, 0xE1, 0x35, 0x6D, 0x6D, 0x51, 0xC2, 0x45,
        0xE4, 0x85, 0xB5, 0x76, 0x62, 0x5E, 0x7E, 0xC6,
        0xF4, 0x4C, 0x42, 0xE9, 0xA6, 0x37, 0xED, 0x6B,
        0x0B, 0xFF, 0x5C, 0xB6, 0xF4, 0x06, 0xB7, 0xED,
        0xEE, 0x38, 0x6B, 0xFB, 0x5A, 0x89, 0x9F, 0xA5,
        0xAE, 0x9F, 0x24, 0x11, 0x7C, 0x4B, 0x1F, 0xE6,
        0x49, 0x28, 0x66, 0x51, 0xEC, 0xE6, 0x53, 0x81,
        0xFF, 0xFF, 0xFF, 0xFF, 0xFF, 0xFF, 0xFF, 0xFF
    };

    int ret;

    if(key_state->state == libssh2_NB_state_idle) {
        /* g == 2 */
        key_state->p = _libssh2_bn_init_from_bin(); /* SSH2 defined value
                                                       (p_value) */
        key_state->g = _libssh2_bn_init();      /* SSH2 defined value (2) */

        /* Initialize P and G */
        _libssh2_bn_set_word(key_state->g, 2);
        _libssh2_bn_from_bin(key_state->p, 128, p_value);

        _libssh2_debug(session, LIBSSH2_TRACE_KEX,
                       "Initiating Diffie-Hellman Group1 Key Exchange");

        key_state->state = libssh2_NB_state_created;
    }
    ret = diffie_hellman_sha1(session, key_state->g, key_state->p, 128,
                              SSH_MSG_KEXDH_INIT, SSH_MSG_KEXDH_REPLY,
                              NULL, 0, &key_state->exchange_state);
    if(ret == LIBSSH2_ERROR_EAGAIN) {
        return ret;
    }

    _libssh2_bn_free(key_state->p);
    key_state->p = NULL;
    _libssh2_bn_free(key_state->g);
    key_state->g = NULL;
    key_state->state = libssh2_NB_state_idle;

    return ret;
}



/* kex_method_diffie_hellman_group14_sha1_key_exchange
 * Diffie-Hellman Group14 Key Exchange using SHA1
 */
static int
kex_method_diffie_hellman_group14_sha1_key_exchange(LIBSSH2_SESSION *session,
                                                    key_exchange_state_low_t
                                                    * key_state)
{
    static const unsigned char p_value[256] = {
        0xFF, 0xFF, 0xFF, 0xFF, 0xFF, 0xFF, 0xFF, 0xFF,
        0xC9, 0x0F, 0xDA, 0xA2, 0x21, 0x68, 0xC2, 0x34,
        0xC4, 0xC6, 0x62, 0x8B, 0x80, 0xDC, 0x1C, 0xD1,
        0x29, 0x02, 0x4E, 0x08, 0x8A, 0x67, 0xCC, 0x74,
        0x02, 0x0B, 0xBE, 0xA6, 0x3B, 0x13, 0x9B, 0x22,
        0x51, 0x4A, 0x08, 0x79, 0x8E, 0x34, 0x04, 0xDD,
        0xEF, 0x95, 0x19, 0xB3, 0xCD, 0x3A, 0x43, 0x1B,
        0x30, 0x2B, 0x0A, 0x6D, 0xF2, 0x5F, 0x14, 0x37,
        0x4F, 0xE1, 0x35, 0x6D, 0x6D, 0x51, 0xC2, 0x45,
        0xE4, 0x85, 0xB5, 0x76, 0x62, 0x5E, 0x7E, 0xC6,
        0xF4, 0x4C, 0x42, 0xE9, 0xA6, 0x37, 0xED, 0x6B,
        0x0B, 0xFF, 0x5C, 0xB6, 0xF4, 0x06, 0xB7, 0xED,
        0xEE, 0x38, 0x6B, 0xFB, 0x5A, 0x89, 0x9F, 0xA5,
        0xAE, 0x9F, 0x24, 0x11, 0x7C, 0x4B, 0x1F, 0xE6,
        0x49, 0x28, 0x66, 0x51, 0xEC, 0xE4, 0x5B, 0x3D,
        0xC2, 0x00, 0x7C, 0xB8, 0xA1, 0x63, 0xBF, 0x05,
        0x98, 0xDA, 0x48, 0x36, 0x1C, 0x55, 0xD3, 0x9A,
        0x69, 0x16, 0x3F, 0xA8, 0xFD, 0x24, 0xCF, 0x5F,
        0x83, 0x65, 0x5D, 0x23, 0xDC, 0xA3, 0xAD, 0x96,
        0x1C, 0x62, 0xF3, 0x56, 0x20, 0x85, 0x52, 0xBB,
        0x9E, 0xD5, 0x29, 0x07, 0x70, 0x96, 0x96, 0x6D,
        0x67, 0x0C, 0x35, 0x4E, 0x4A, 0xBC, 0x98, 0x04,
        0xF1, 0x74, 0x6C, 0x08, 0xCA, 0x18, 0x21, 0x7C,
        0x32, 0x90, 0x5E, 0x46, 0x2E, 0x36, 0xCE, 0x3B,
        0xE3, 0x9E, 0x77, 0x2C, 0x18, 0x0E, 0x86, 0x03,
        0x9B, 0x27, 0x83, 0xA2, 0xEC, 0x07, 0xA2, 0x8F,
        0xB5, 0xC5, 0x5D, 0xF0, 0x6F, 0x4C, 0x52, 0xC9,
        0xDE, 0x2B, 0xCB, 0xF6, 0x95, 0x58, 0x17, 0x18,
        0x39, 0x95, 0x49, 0x7C, 0xEA, 0x95, 0x6A, 0xE5,
        0x15, 0xD2, 0x26, 0x18, 0x98, 0xFA, 0x05, 0x10,
        0x15, 0x72, 0x8E, 0x5A, 0x8A, 0xAC, 0xAA, 0x68,
        0xFF, 0xFF, 0xFF, 0xFF, 0xFF, 0xFF, 0xFF, 0xFF
    };
    int ret;

    if(key_state->state == libssh2_NB_state_idle) {
        key_state->p = _libssh2_bn_init_from_bin(); /* SSH2 defined value
                                                       (p_value) */
        key_state->g = _libssh2_bn_init();      /* SSH2 defined value (2) */

        /* g == 2 */
        /* Initialize P and G */
        _libssh2_bn_set_word(key_state->g, 2);
        _libssh2_bn_from_bin(key_state->p, 256, p_value);

        _libssh2_debug(session, LIBSSH2_TRACE_KEX,
                       "Initiating Diffie-Hellman Group14 Key Exchange");

        key_state->state = libssh2_NB_state_created;
    }
    ret = diffie_hellman_sha1(session, key_state->g, key_state->p,
                              256, SSH_MSG_KEXDH_INIT, SSH_MSG_KEXDH_REPLY,
                              NULL, 0, &key_state->exchange_state);
    if(ret == LIBSSH2_ERROR_EAGAIN) {
        return ret;
    }

    key_state->state = libssh2_NB_state_idle;
    _libssh2_bn_free(key_state->p);
    key_state->p = NULL;
    _libssh2_bn_free(key_state->g);
    key_state->g = NULL;

    return ret;
}



/* kex_method_diffie_hellman_group_exchange_sha1_key_exchange
 * Diffie-Hellman Group Exchange Key Exchange using SHA1
 * Negotiates random(ish) group for secret derivation
 */
static int
kex_method_diffie_hellman_group_exchange_sha1_key_exchange
(LIBSSH2_SESSION * session, key_exchange_state_low_t * key_state)
{
    int ret = 0;
    int rc;

    if(key_state->state == libssh2_NB_state_idle) {
        key_state->p = _libssh2_bn_init_from_bin();
        key_state->g = _libssh2_bn_init_from_bin();
        /* Ask for a P and G pair */
#ifdef LIBSSH2_DH_GEX_NEW
        key_state->request[0] = SSH_MSG_KEX_DH_GEX_REQUEST;
        _libssh2_htonu32(key_state->request + 1, LIBSSH2_DH_GEX_MINGROUP);
        _libssh2_htonu32(key_state->request + 5, LIBSSH2_DH_GEX_OPTGROUP);
        _libssh2_htonu32(key_state->request + 9, LIBSSH2_DH_GEX_MAXGROUP);
        key_state->request_len = 13;
        _libssh2_debug(session, LIBSSH2_TRACE_KEX,
                       "Initiating Diffie-Hellman Group-Exchange "
                       "(New Method)");
#else
        key_state->request[0] = SSH_MSG_KEX_DH_GEX_REQUEST_OLD;
        _libssh2_htonu32(key_state->request + 1, LIBSSH2_DH_GEX_OPTGROUP);
        key_state->request_len = 5;
        _libssh2_debug(session, LIBSSH2_TRACE_KEX,
                       "Initiating Diffie-Hellman Group-Exchange "
                       "(Old Method)");
#endif

        key_state->state = libssh2_NB_state_created;
    }

    if(key_state->state == libssh2_NB_state_created) {
        rc = _libssh2_transport_send(session, key_state->request,
                                     key_state->request_len, NULL, 0);
        if(rc == LIBSSH2_ERROR_EAGAIN) {
            return rc;
        }
        else if(rc) {
            ret = _libssh2_error(session, rc,
                                 "Unable to send Group Exchange Request");
            goto dh_gex_clean_exit;
        }

        key_state->state = libssh2_NB_state_sent;
    }

    if(key_state->state == libssh2_NB_state_sent) {
        rc = _libssh2_packet_require(session, SSH_MSG_KEX_DH_GEX_GROUP,
                                     &key_state->data, &key_state->data_len,
                                     0, NULL, 0, &key_state->req_state);
        if(rc == LIBSSH2_ERROR_EAGAIN) {
            return rc;
        }
        else if(rc) {
            ret = _libssh2_error(session, rc,
                                 "Timeout waiting for GEX_GROUP reply");
            goto dh_gex_clean_exit;
        }

        key_state->state = libssh2_NB_state_sent1;
    }

    if(key_state->state == libssh2_NB_state_sent1) {
        size_t p_len, g_len;
        unsigned char *p, *g;
        struct string_buf buf;

        if(key_state->data_len < 9) {
            ret = _libssh2_error(session, LIBSSH2_ERROR_PROTO,
                                 "Unexpected key length");
            goto dh_gex_clean_exit;
        }

        buf.data = key_state->data;
        buf.dataptr = buf.data;
        buf.len = key_state->data_len;

        buf.dataptr++; /* increment to big num */

        if(_libssh2_get_bignum_bytes(&buf, &p, &p_len)) {
            ret = _libssh2_error(session, LIBSSH2_ERROR_PROTO,
                                 "Unexpected value");
            goto dh_gex_clean_exit;
        }

        if(_libssh2_get_bignum_bytes(&buf, &g, &g_len)) {
            ret = _libssh2_error(session, LIBSSH2_ERROR_PROTO,
                                 "Unexpected value");
            goto dh_gex_clean_exit;
        }

        _libssh2_bn_from_bin(key_state->p, p_len, p);
        _libssh2_bn_from_bin(key_state->g, g_len, g);

        ret = diffie_hellman_sha1(session, key_state->g, key_state->p, p_len,
                                  SSH_MSG_KEX_DH_GEX_INIT,
                                  SSH_MSG_KEX_DH_GEX_REPLY,
                                  key_state->data + 1,
                                  key_state->data_len - 1,
                                  &key_state->exchange_state);
        if(ret == LIBSSH2_ERROR_EAGAIN) {
            return ret;
        }

        LIBSSH2_FREE(session, key_state->data);
    }

  dh_gex_clean_exit:
    key_state->state = libssh2_NB_state_idle;
    _libssh2_bn_free(key_state->g);
    key_state->g = NULL;
    _libssh2_bn_free(key_state->p);
    key_state->p = NULL;

    return ret;
}



/* kex_method_diffie_hellman_group_exchange_sha256_key_exchange
 * Diffie-Hellman Group Exchange Key Exchange using SHA256
 * Negotiates random(ish) group for secret derivation
 */
static int
kex_method_diffie_hellman_group_exchange_sha256_key_exchange
(LIBSSH2_SESSION * session, key_exchange_state_low_t * key_state)
{
    int ret = 0;
    int rc;

    if(key_state->state == libssh2_NB_state_idle) {
        key_state->p = _libssh2_bn_init();
        key_state->g = _libssh2_bn_init();
        /* Ask for a P and G pair */
#ifdef LIBSSH2_DH_GEX_NEW
        key_state->request[0] = SSH_MSG_KEX_DH_GEX_REQUEST;
        _libssh2_htonu32(key_state->request + 1, LIBSSH2_DH_GEX_MINGROUP);
        _libssh2_htonu32(key_state->request + 5, LIBSSH2_DH_GEX_OPTGROUP);
        _libssh2_htonu32(key_state->request + 9, LIBSSH2_DH_GEX_MAXGROUP);
        key_state->request_len = 13;
        _libssh2_debug(session, LIBSSH2_TRACE_KEX,
                       "Initiating Diffie-Hellman Group-Exchange "
                       "(New Method SHA256)");
#else
        key_state->request[0] = SSH_MSG_KEX_DH_GEX_REQUEST_OLD;
        _libssh2_htonu32(key_state->request + 1, LIBSSH2_DH_GEX_OPTGROUP);
        key_state->request_len = 5;
        _libssh2_debug(session, LIBSSH2_TRACE_KEX,
                       "Initiating Diffie-Hellman Group-Exchange "
                       "(Old Method SHA256)");
#endif

        key_state->state = libssh2_NB_state_created;
    }

    if(key_state->state == libssh2_NB_state_created) {
        rc = _libssh2_transport_send(session, key_state->request,
                                     key_state->request_len, NULL, 0);
        if(rc == LIBSSH2_ERROR_EAGAIN) {
            return rc;
        }
        else if(rc) {
            ret = _libssh2_error(session, rc,
                                 "Unable to send "
                                 "Group Exchange Request SHA256");
            goto dh_gex_clean_exit;
        }

        key_state->state = libssh2_NB_state_sent;
    }

    if(key_state->state == libssh2_NB_state_sent) {
        rc = _libssh2_packet_require(session, SSH_MSG_KEX_DH_GEX_GROUP,
                                     &key_state->data, &key_state->data_len,
                                     0, NULL, 0, &key_state->req_state);
        if(rc == LIBSSH2_ERROR_EAGAIN) {
            return rc;
        }
        else if(rc) {
            ret = _libssh2_error(session, rc,
                                 "Timeout waiting for GEX_GROUP reply SHA256");
            goto dh_gex_clean_exit;
        }

        key_state->state = libssh2_NB_state_sent1;
    }

    if(key_state->state == libssh2_NB_state_sent1) {
        unsigned char *p, *g;
        size_t p_len, g_len;
        struct string_buf buf;

        if(key_state->data_len < 9) {
            ret = _libssh2_error(session, LIBSSH2_ERROR_PROTO,
                                 "Unexpected key length");
            goto dh_gex_clean_exit;
        }

        buf.data = key_state->data;
        buf.dataptr = buf.data;
        buf.len = key_state->data_len;

        buf.dataptr++; /* increment to big num */

        if(_libssh2_get_bignum_bytes(&buf, &p, &p_len)) {
            ret = _libssh2_error(session, LIBSSH2_ERROR_PROTO,
                                 "Unexpected value");
            goto dh_gex_clean_exit;
        }

        if(_libssh2_get_bignum_bytes(&buf, &g, &g_len)) {
            ret = _libssh2_error(session, LIBSSH2_ERROR_PROTO,
                                 "Unexpected value");
            goto dh_gex_clean_exit;
        }

        _libssh2_bn_from_bin(key_state->p, p_len, p);
        _libssh2_bn_from_bin(key_state->g, g_len, g);

        ret = diffie_hellman_sha256(session, key_state->g, key_state->p, p_len,
                                    SSH_MSG_KEX_DH_GEX_INIT,
                                    SSH_MSG_KEX_DH_GEX_REPLY,
                                    key_state->data + 1,
                                    key_state->data_len - 1,
                                    &key_state->exchange_state);
        if(ret == LIBSSH2_ERROR_EAGAIN) {
            return ret;
        }

        LIBSSH2_FREE(session, key_state->data);
    }

  dh_gex_clean_exit:
    key_state->state = libssh2_NB_state_idle;
    _libssh2_bn_free(key_state->g);
    key_state->g = NULL;
    _libssh2_bn_free(key_state->p);
    key_state->p = NULL;

    return ret;
}


#if LIBSSH2_ECDSA

/* kex_session_ecdh_curve_type
 * returns the EC curve type by name used in key exchange
 */

static int
kex_session_ecdh_curve_type(const char *name, libssh2_curve_type *out_type)
{
    int ret = 0;
    libssh2_curve_type type;

    if(name == NULL)
        return -1;

    if(strcmp(name, "ecdh-sha2-nistp256") == 0)
        type = LIBSSH2_EC_CURVE_NISTP256;
    else if(strcmp(name, "ecdh-sha2-nistp384") == 0)
        type = LIBSSH2_EC_CURVE_NISTP384;
    else if(strcmp(name, "ecdh-sha2-nistp521") == 0)
        type = LIBSSH2_EC_CURVE_NISTP521;
    else {
        ret = -1;
    }

    if(ret == 0 && out_type) {
        *out_type = type;
    }

    return ret;
}


/* LIBSSH2_KEX_METHOD_EC_SHA_HASH_CREATE_VERIFY
 *
 * Macro that create and verifies EC SHA hash with a given digest bytes
 *
 * Payload format:
 *
 * string   V_C, client's identification string (CR and LF excluded)
 * string   V_S, server's identification string (CR and LF excluded)
 * string   I_C, payload of the client's SSH_MSG_KEXINIT
 * string   I_S, payload of the server's SSH_MSG_KEXINIT
 * string   K_S, server's public host key
 * string   Q_C, client's ephemeral public key octet string
 * string   Q_S, server's ephemeral public key octet string
 * mpint    K,   shared secret
 *
 */

#define LIBSSH2_KEX_METHOD_EC_SHA_HASH_CREATE_VERIFY(digest_type)       \
{                                                                       \
    libssh2_sha##digest_type##_ctx ctx;                                 \
    exchange_state->exchange_hash = (void *)&ctx;                       \
    libssh2_sha##digest_type##_init(&ctx);                              \
    if(session->local.banner) {                                         \
        _libssh2_htonu32(exchange_state->h_sig_comp,                    \
                         strlen((char *) session->local.banner) - 2);   \
        libssh2_sha##digest_type##_update(ctx,                          \
                                          exchange_state->h_sig_comp, 4); \
        libssh2_sha##digest_type##_update(ctx,                          \
                                          (char *) session->local.banner, \
                                          strlen((char *)               \
                                                 session->local.banner) \
                                          - 2);                         \
    }                                                                   \
    else {                                                              \
        _libssh2_htonu32(exchange_state->h_sig_comp,                    \
                         sizeof(LIBSSH2_SSH_DEFAULT_BANNER) - 1);       \
        libssh2_sha##digest_type##_update(ctx,                          \
                                          exchange_state->h_sig_comp, 4); \
        libssh2_sha##digest_type##_update(ctx,                          \
                                          LIBSSH2_SSH_DEFAULT_BANNER,   \
                                          sizeof(LIBSSH2_SSH_DEFAULT_BANNER) \
                                          - 1);                         \
    }                                                                   \
                                                                        \
    _libssh2_htonu32(exchange_state->h_sig_comp,                        \
                     strlen((char *) session->remote.banner));          \
    libssh2_sha##digest_type##_update(ctx,                              \
                                      exchange_state->h_sig_comp, 4);   \
    libssh2_sha##digest_type##_update(ctx,                              \
                                      session->remote.banner,           \
                                      strlen((char *)                   \
                                             session->remote.banner));  \
                                                                        \
    _libssh2_htonu32(exchange_state->h_sig_comp,                        \
                     session->local.kexinit_len);                       \
    libssh2_sha##digest_type##_update(ctx,                              \
                                      exchange_state->h_sig_comp, 4);   \
    libssh2_sha##digest_type##_update(ctx,                              \
                                      session->local.kexinit,           \
                                      session->local.kexinit_len);      \
                                                                        \
    _libssh2_htonu32(exchange_state->h_sig_comp,                        \
                     session->remote.kexinit_len);                      \
    libssh2_sha##digest_type##_update(ctx,                              \
                                      exchange_state->h_sig_comp, 4);   \
    libssh2_sha##digest_type##_update(ctx,                              \
                                      session->remote.kexinit,          \
                                      session->remote.kexinit_len);     \
                                                                        \
    _libssh2_htonu32(exchange_state->h_sig_comp,                        \
                     session->server_hostkey_len);                      \
    libssh2_sha##digest_type##_update(ctx,                              \
                                      exchange_state->h_sig_comp, 4);   \
    libssh2_sha##digest_type##_update(ctx,                              \
                                      session->server_hostkey,          \
                                      session->server_hostkey_len);     \
                                                                        \
    _libssh2_htonu32(exchange_state->h_sig_comp,                        \
                     public_key_len);                                   \
    libssh2_sha##digest_type##_update(ctx,                              \
                                      exchange_state->h_sig_comp, 4);   \
    libssh2_sha##digest_type##_update(ctx,                              \
                                      public_key,                       \
                                      public_key_len);                  \
                                                                        \
    _libssh2_htonu32(exchange_state->h_sig_comp,                        \
                     server_public_key_len);                            \
    libssh2_sha##digest_type##_update(ctx,                              \
                                      exchange_state->h_sig_comp, 4);   \
    libssh2_sha##digest_type##_update(ctx,                              \
                                      server_public_key,                \
                                      server_public_key_len);           \
                                                                        \
    libssh2_sha##digest_type##_update(ctx,                              \
                                      exchange_state->k_value,          \
                                      exchange_state->k_value_len);     \
                                                                        \
    libssh2_sha##digest_type##_final(ctx, exchange_state->h_sig_comp);  \
                                                                        \
    if(session->hostkey->                                               \
       sig_verify(session, exchange_state->h_sig,                       \
                  exchange_state->h_sig_len, exchange_state->h_sig_comp, \
                  SHA##digest_type##_DIGEST_LENGTH,                     \
                  &session->server_hostkey_abstract)) {                 \
        rc = -1;                                                        \
    }                                                                   \
}                                                                       \


/* ecdh_sha2_nistp
 * Elliptic Curve Diffie Hellman Key Exchange
 */

static int ecdh_sha2_nistp(LIBSSH2_SESSION *session, libssh2_curve_type type,
                           unsigned char *data, size_t data_len,
                           unsigned char *public_key,
                           size_t public_key_len, _libssh2_ec_key *private_key,
                           kmdhgGPshakex_state_t *exchange_state)
{
    int ret = 0;
    int rc;

    if(data_len < 5) {
        ret = _libssh2_error(session, LIBSSH2_ERROR_HOSTKEY_INIT,
                            "Host key data is too short");
        return ret;
    }

    if(exchange_state->state == libssh2_NB_state_idle) {

        /* Setup initial values */
        exchange_state->k = _libssh2_bn_init();

        exchange_state->state = libssh2_NB_state_created;
    }

    if(exchange_state->state == libssh2_NB_state_created) {
        /* parse INIT reply data */

        /* host key K_S */
        unsigned char *s = data + 1; /* Advance past packet type */
        unsigned char *server_public_key;
        size_t server_public_key_len;
        size_t host_sig_len;

        session->server_hostkey_len =
            _libssh2_ntohu32((const unsigned char *)s);
        s += 4;

        session->server_hostkey = LIBSSH2_ALLOC(session,
                                                session->server_hostkey_len);
        if(!session->server_hostkey) {
            ret = _libssh2_error(session, LIBSSH2_ERROR_ALLOC,
                                 "Unable to allocate memory for a copy "
                                 "of the host key");
            goto clean_exit;
        }

        memcpy(session->server_hostkey, s, session->server_hostkey_len);
        s += session->server_hostkey_len;

#if LIBSSH2_MD5
        {
            libssh2_md5_ctx fingerprint_ctx;

            if(libssh2_md5_init(&fingerprint_ctx)) {
                libssh2_md5_update(fingerprint_ctx, session->server_hostkey,
                                   session->server_hostkey_len);
                libssh2_md5_final(fingerprint_ctx,
                                  session->server_hostkey_md5);
                session->server_hostkey_md5_valid = TRUE;
            }
            else {
                session->server_hostkey_md5_valid = FALSE;
            }
        }
#ifdef LIBSSH2DEBUG
        {
            char fingerprint[50], *fprint = fingerprint;
            int i;
            for(i = 0; i < 16; i++, fprint += 3) {
                snprintf(fprint, 4, "%02x:", session->server_hostkey_md5[i]);
            }
            *(--fprint) = '\0';
            _libssh2_debug(session, LIBSSH2_TRACE_KEX,
                           "Server's MD5 Fingerprint: %s", fingerprint);
        }
#endif /* LIBSSH2DEBUG */
#endif /* ! LIBSSH2_MD5 */

        {
            libssh2_sha1_ctx fingerprint_ctx;

            if(libssh2_sha1_init(&fingerprint_ctx)) {
                libssh2_sha1_update(fingerprint_ctx, session->server_hostkey,
                                    session->server_hostkey_len);
                libssh2_sha1_final(fingerprint_ctx,
                                   session->server_hostkey_sha1);
                session->server_hostkey_sha1_valid = TRUE;
            }
            else {
                session->server_hostkey_sha1_valid = FALSE;
            }
        }
#ifdef LIBSSH2DEBUG
        {
            char fingerprint[64], *fprint = fingerprint;
            int i;

            for(i = 0; i < 20; i++, fprint += 3) {
                snprintf(fprint, 4, "%02x:", session->server_hostkey_sha1[i]);
            }
            *(--fprint) = '\0';
            _libssh2_debug(session, LIBSSH2_TRACE_KEX,
                           "Server's SHA1 Fingerprint: %s", fingerprint);
        }
#endif /* LIBSSH2DEBUG */

        /* SHA256 */
        {
            libssh2_sha256_ctx fingerprint_ctx;

            if(libssh2_sha256_init(&fingerprint_ctx)) {
                libssh2_sha256_update(fingerprint_ctx, session->server_hostkey,
                                      session->server_hostkey_len);
                libssh2_sha256_final(fingerprint_ctx,
                                     session->server_hostkey_sha256);
                session->server_hostkey_sha256_valid = TRUE;
            }
            else {
                session->server_hostkey_sha256_valid = FALSE;
            }
        }
#ifdef LIBSSH2DEBUG
        {
            char *base64Fingerprint = NULL;
            _libssh2_base64_encode(session,
                                   (const char *)
                                   session->server_hostkey_sha256,
                                   SHA256_DIGEST_LENGTH, &base64Fingerprint);
            if(base64Fingerprint != NULL) {
                _libssh2_debug(session, LIBSSH2_TRACE_KEX,
                               "Server's SHA256 Fingerprint: %s",
                               base64Fingerprint);
                LIBSSH2_FREE(session, base64Fingerprint);
            }
        }
#endif /* LIBSSH2DEBUG */

        if(session->hostkey->init(session, session->server_hostkey,
                                   session->server_hostkey_len,
                                   &session->server_hostkey_abstract)) {
            ret = _libssh2_error(session, LIBSSH2_ERROR_HOSTKEY_INIT,
                                 "Unable to initialize hostkey importer");
            goto clean_exit;
        }

        /* server public key Q_S */
        server_public_key_len = _libssh2_ntohu32((const unsigned char *)s);
        s += 4;

        server_public_key = s;
        s += server_public_key_len;

        /* server signature */
        host_sig_len = _libssh2_ntohu32((const unsigned char *)s);
        s += 4;

        exchange_state->h_sig = s;
        exchange_state->h_sig_len = host_sig_len;
        s += host_sig_len;

        /* Compute the shared secret K */
        rc = _libssh2_ecdh_gen_k(&exchange_state->k, private_key,
                                 server_public_key, server_public_key_len);
        if(rc != 0) {
            ret = _libssh2_error(session, LIBSSH2_ERROR_KEX_FAILURE,
                                 "Unable to create ECDH shared secret");
            goto clean_exit;
        }

        exchange_state->k_value_len = _libssh2_bn_bytes(exchange_state->k) + 5;
        if(_libssh2_bn_bits(exchange_state->k) % 8) {
            /* don't need leading 00 */
            exchange_state->k_value_len--;
        }
        exchange_state->k_value =
        LIBSSH2_ALLOC(session, exchange_state->k_value_len);
        if(!exchange_state->k_value) {
            ret = _libssh2_error(session, LIBSSH2_ERROR_ALLOC,
                                 "Unable to allocate buffer for K");
            goto clean_exit;
        }
        _libssh2_htonu32(exchange_state->k_value,
                         exchange_state->k_value_len - 4);
        if(_libssh2_bn_bits(exchange_state->k) % 8) {
            _libssh2_bn_to_bin(exchange_state->k, exchange_state->k_value + 4);
        }
        else {
            exchange_state->k_value[4] = 0;
            _libssh2_bn_to_bin(exchange_state->k, exchange_state->k_value + 5);
        }

        /* verify hash */

        switch(type) {
            case LIBSSH2_EC_CURVE_NISTP256:
                LIBSSH2_KEX_METHOD_EC_SHA_HASH_CREATE_VERIFY(256);
                break;

            case LIBSSH2_EC_CURVE_NISTP384:
                LIBSSH2_KEX_METHOD_EC_SHA_HASH_CREATE_VERIFY(384);
                break;
            case LIBSSH2_EC_CURVE_NISTP521:
                LIBSSH2_KEX_METHOD_EC_SHA_HASH_CREATE_VERIFY(512);
                break;
        }

        if(rc != 0) {
            ret = _libssh2_error(session, LIBSSH2_ERROR_HOSTKEY_SIGN,
                                 "Unable to verify hostkey signature");
            goto clean_exit;
        }

        exchange_state->c = SSH_MSG_NEWKEYS;
        exchange_state->state = libssh2_NB_state_sent;
    }

    if(exchange_state->state == libssh2_NB_state_sent) {
        rc = _libssh2_transport_send(session, &exchange_state->c, 1, NULL, 0);
        if(rc == LIBSSH2_ERROR_EAGAIN) {
            return rc;
        }
        else if(rc) {
            ret = _libssh2_error(session, rc,
                                 "Unable to send NEWKEYS message");
            goto clean_exit;
        }

        exchange_state->state = libssh2_NB_state_sent2;
    }

    if(exchange_state->state == libssh2_NB_state_sent2) {
        rc = _libssh2_packet_require(session, SSH_MSG_NEWKEYS,
                                     &exchange_state->tmp,
                                     &exchange_state->tmp_len, 0, NULL, 0,
                                     &exchange_state->req_state);
        if(rc == LIBSSH2_ERROR_EAGAIN) {
            return rc;
        }
        else if(rc) {
            ret = _libssh2_error(session, rc, "Timed out waiting for NEWKEYS");
            goto clean_exit;
        }

        /* The first key exchange has been performed,
         switch to active crypt/comp/mac mode */
        session->state |= LIBSSH2_STATE_NEWKEYS;
        _libssh2_debug(session, LIBSSH2_TRACE_KEX, "Received NEWKEYS message");

        /* This will actually end up being just packet_type(1)
         for this packet type anyway */
        LIBSSH2_FREE(session, exchange_state->tmp);

        if(!session->session_id) {

            size_t digest_length = 0;

            if(type == LIBSSH2_EC_CURVE_NISTP256)
                digest_length = SHA256_DIGEST_LENGTH;
            else if(type == LIBSSH2_EC_CURVE_NISTP384)
                digest_length = SHA384_DIGEST_LENGTH;
            else if(type == LIBSSH2_EC_CURVE_NISTP521)
                digest_length = SHA512_DIGEST_LENGTH;
            else{
                ret = _libssh2_error(session, LIBSSH2_ERROR_KEX_FAILURE,
                                     "Unknown SHA digest for EC curve");
                goto clean_exit;

            }
            session->session_id = LIBSSH2_ALLOC(session, digest_length);
            if(!session->session_id) {
                ret = _libssh2_error(session, LIBSSH2_ERROR_ALLOC,
                                     "Unable to allocate buffer for "
                                     "SHA digest");
                goto clean_exit;
            }
            memcpy(session->session_id, exchange_state->h_sig_comp,
                   digest_length);
             session->session_id_len = digest_length;
            _libssh2_debug(session, LIBSSH2_TRACE_KEX,
                           "session_id calculated");
        }

        /* Cleanup any existing cipher */
        if(session->local.crypt->dtor) {
            session->local.crypt->dtor(session,
                                       &session->local.crypt_abstract);
        }

        /* Calculate IV/Secret/Key for each direction */
        if(session->local.crypt->init) {
            unsigned char *iv = NULL, *secret = NULL;
            int free_iv = 0, free_secret = 0;

            LIBSSH2_KEX_METHOD_EC_SHA_VALUE_HASH(iv,
                                                 session->local.crypt->
                                                 iv_len, "A");
            if(!iv) {
                ret = -1;
                goto clean_exit;
            }

            LIBSSH2_KEX_METHOD_EC_SHA_VALUE_HASH(secret,
                                                session->local.crypt->
                                                secret_len, "C");

            if(!secret) {
                LIBSSH2_FREE(session, iv);
                ret = LIBSSH2_ERROR_KEX_FAILURE;
                goto clean_exit;
            }
            if(session->local.crypt->
                init(session, session->local.crypt, iv, &free_iv, secret,
                     &free_secret, 1, &session->local.crypt_abstract)) {
                    LIBSSH2_FREE(session, iv);
                    LIBSSH2_FREE(session, secret);
                    ret = LIBSSH2_ERROR_KEX_FAILURE;
                    goto clean_exit;
                }

            if(free_iv) {
                _libssh2_explicit_zero(iv, session->local.crypt->iv_len);
                LIBSSH2_FREE(session, iv);
            }

            if(free_secret) {
                _libssh2_explicit_zero(secret,
                                       session->local.crypt->secret_len);
                LIBSSH2_FREE(session, secret);
            }
        }
        _libssh2_debug(session, LIBSSH2_TRACE_KEX,
                       "Client to Server IV and Key calculated");

        if(session->remote.crypt->dtor) {
            /* Cleanup any existing cipher */
            session->remote.crypt->dtor(session,
                                        &session->remote.crypt_abstract);
        }

        if(session->remote.crypt->init) {
            unsigned char *iv = NULL, *secret = NULL;
            int free_iv = 0, free_secret = 0;

            LIBSSH2_KEX_METHOD_EC_SHA_VALUE_HASH(iv,
                                                 session->remote.crypt->
                                                 iv_len, "B");

            if(!iv) {
                ret = LIBSSH2_ERROR_KEX_FAILURE;
                goto clean_exit;
            }
            LIBSSH2_KEX_METHOD_EC_SHA_VALUE_HASH(secret,
                                                 session->remote.crypt->
                                                 secret_len, "D");

            if(!secret) {
                LIBSSH2_FREE(session, iv);
                ret = LIBSSH2_ERROR_KEX_FAILURE;
                goto clean_exit;
            }
            if(session->remote.crypt->
                init(session, session->remote.crypt, iv, &free_iv, secret,
                     &free_secret, 0, &session->remote.crypt_abstract)) {
                    LIBSSH2_FREE(session, iv);
                    LIBSSH2_FREE(session, secret);
                    ret = LIBSSH2_ERROR_KEX_FAILURE;
                    goto clean_exit;
                }

            if(free_iv) {
                _libssh2_explicit_zero(iv, session->remote.crypt->iv_len);
                LIBSSH2_FREE(session, iv);
            }

            if(free_secret) {
                _libssh2_explicit_zero(secret,
                                       session->remote.crypt->secret_len);
                LIBSSH2_FREE(session, secret);
            }
        }
        _libssh2_debug(session, LIBSSH2_TRACE_KEX,
                       "Server to Client IV and Key calculated");

        if(session->local.mac->dtor) {
            session->local.mac->dtor(session, &session->local.mac_abstract);
        }

        if(session->local.mac->init) {
            unsigned char *key = NULL;
            int free_key = 0;

            LIBSSH2_KEX_METHOD_EC_SHA_VALUE_HASH(key,
                                                 session->local.mac->
                                                 key_len, "E");

            if(!key) {
                ret = LIBSSH2_ERROR_KEX_FAILURE;
                goto clean_exit;
            }
            session->local.mac->init(session, key, &free_key,
                                     &session->local.mac_abstract);

            if(free_key) {
                _libssh2_explicit_zero(key, session->local.mac->key_len);
                LIBSSH2_FREE(session, key);
            }
        }
        _libssh2_debug(session, LIBSSH2_TRACE_KEX,
                       "Client to Server HMAC Key calculated");

        if(session->remote.mac->dtor) {
            session->remote.mac->dtor(session, &session->remote.mac_abstract);
        }

        if(session->remote.mac->init) {
            unsigned char *key = NULL;
            int free_key = 0;

            LIBSSH2_KEX_METHOD_EC_SHA_VALUE_HASH(key,
                                                 session->remote.mac->
                                                 key_len, "F");

            if(!key) {
                ret = LIBSSH2_ERROR_KEX_FAILURE;
                goto clean_exit;
            }
            session->remote.mac->init(session, key, &free_key,
                                      &session->remote.mac_abstract);

            if(free_key) {
                _libssh2_explicit_zero(key, session->remote.mac->key_len);
                LIBSSH2_FREE(session, key);
            }
        }
        _libssh2_debug(session, LIBSSH2_TRACE_KEX,
                       "Server to Client HMAC Key calculated");

        /* Initialize compression for each direction */

        /* Cleanup any existing compression */
        if(session->local.comp && session->local.comp->dtor) {
            session->local.comp->dtor(session, 1,
                                      &session->local.comp_abstract);
        }

        if(session->local.comp && session->local.comp->init) {
            if(session->local.comp->init(session, 1,
                                          &session->local.comp_abstract)) {
                ret = LIBSSH2_ERROR_KEX_FAILURE;
                goto clean_exit;
            }
        }
        _libssh2_debug(session, LIBSSH2_TRACE_KEX,
                       "Client to Server compression initialized");

        if(session->remote.comp && session->remote.comp->dtor) {
            session->remote.comp->dtor(session, 0,
                                       &session->remote.comp_abstract);
        }

        if(session->remote.comp && session->remote.comp->init) {
            if(session->remote.comp->init(session, 0,
                                           &session->remote.comp_abstract)) {
                ret = LIBSSH2_ERROR_KEX_FAILURE;
                goto clean_exit;
            }
        }
        _libssh2_debug(session, LIBSSH2_TRACE_KEX,
                       "Server to Client compression initialized");

    }

clean_exit:
    _libssh2_bn_free(exchange_state->k);
    exchange_state->k = NULL;

    if(exchange_state->k_value) {
        LIBSSH2_FREE(session, exchange_state->k_value);
        exchange_state->k_value = NULL;
    }

    exchange_state->state = libssh2_NB_state_idle;

    return ret;
}

/* kex_method_ecdh_key_exchange
 *
 * Elliptic Curve Diffie Hellman Key Exchange
 * supports SHA256/384/512 hashes based on negotated ecdh method
 *
 */

static int
kex_method_ecdh_key_exchange
(LIBSSH2_SESSION * session, key_exchange_state_low_t * key_state)
{
    int ret = 0;
    int rc = 0;
    unsigned char *s;
    libssh2_curve_type type;

    if(key_state->state == libssh2_NB_state_idle) {

        key_state->public_key_oct = NULL;
        key_state->state = libssh2_NB_state_created;
    }

    if(key_state->state == libssh2_NB_state_created) {
        rc = kex_session_ecdh_curve_type(session->kex->name, &type);

        if(rc != 0) {
            ret = _libssh2_error(session, -1,
                                 "Unknown KEX nistp curve type");
            goto ecdh_clean_exit;
        }

        rc = _libssh2_ecdsa_create_key(session, &key_state->private_key,
                                       &key_state->public_key_oct,
                                       &key_state->public_key_oct_len, type);

        if(rc != 0) {
            ret = _libssh2_error(session, rc,
                                 "Unable to create private key");
            goto ecdh_clean_exit;
        }

        key_state->request[0] = SSH2_MSG_KEX_ECDH_INIT;
        s = key_state->request + 1;
        _libssh2_store_str(&s, (const char *)key_state->public_key_oct,
                           key_state->public_key_oct_len);
        key_state->request_len = key_state->public_key_oct_len + 5;

        _libssh2_debug(session, LIBSSH2_TRACE_KEX,
                       "Initiating ECDH SHA2 NISTP256");

        key_state->state = libssh2_NB_state_sent;
    }

    if(key_state->state == libssh2_NB_state_sent) {
        rc = _libssh2_transport_send(session, key_state->request,
                                     key_state->request_len, NULL, 0);
        if(rc == LIBSSH2_ERROR_EAGAIN) {
            return rc;
        }
        else if(rc) {
            ret = _libssh2_error(session, rc,
                                 "Unable to send ECDH_INIT");
            goto ecdh_clean_exit;
        }

        key_state->state = libssh2_NB_state_sent1;
    }

    if(key_state->state == libssh2_NB_state_sent1) {
        rc = _libssh2_packet_require(session, SSH2_MSG_KEX_ECDH_REPLY,
                                     &key_state->data, &key_state->data_len,
                                     0, NULL, 0, &key_state->req_state);
        if(rc == LIBSSH2_ERROR_EAGAIN) {
            return rc;
        }
        else if(rc) {
            ret = _libssh2_error(session, rc,
                                 "Timeout waiting for ECDH_REPLY reply");
            goto ecdh_clean_exit;
        }

        key_state->state = libssh2_NB_state_sent2;
    }

    if(key_state->state == libssh2_NB_state_sent2) {

        (void)kex_session_ecdh_curve_type(session->kex->name, &type);

        ret = ecdh_sha2_nistp(session, type, key_state->data,
                              key_state->data_len,
                              (unsigned char *)key_state->public_key_oct,
                              key_state->public_key_oct_len,
                              key_state->private_key,
                              &key_state->exchange_state);

        if(ret == LIBSSH2_ERROR_EAGAIN) {
            return ret;
        }

        LIBSSH2_FREE(session, key_state->data);
    }

ecdh_clean_exit:

    if(key_state->public_key_oct) {
        LIBSSH2_FREE(session, key_state->public_key_oct);
        key_state->public_key_oct = NULL;
    }

    if(key_state->private_key) {
        _libssh2_ecdsa_free(key_state->private_key);
        key_state->private_key = NULL;
    }

    key_state->state = libssh2_NB_state_idle;

    return ret;
}

#endif /*LIBSSH2_ECDSA*/


#if LIBSSH2_ED25519

/* curve25519_sha256
 * Elliptic Curve Key Exchange
 */

static int
curve25519_sha256(LIBSSH2_SESSION *session, unsigned char *data,
                  size_t data_len,
                  unsigned char public_key[LIBSSH2_ED25519_KEY_LEN],
                  unsigned char private_key[LIBSSH2_ED25519_KEY_LEN],
                  kmdhgGPshakex_state_t *exchange_state)
{
    int ret = 0;
    int rc;
    int public_key_len = LIBSSH2_ED25519_KEY_LEN;

    if(data_len < 5) {
        return _libssh2_error(session, LIBSSH2_ERROR_HOSTKEY_INIT,
                              "Data is too short");
    }

    if(exchange_state->state == libssh2_NB_state_idle) {

        /* Setup initial values */
        exchange_state->k = _libssh2_bn_init();

        exchange_state->state = libssh2_NB_state_created;
    }

    if(exchange_state->state == libssh2_NB_state_created) {
        /* parse INIT reply data */
        unsigned char *server_public_key, *server_host_key;
        size_t server_public_key_len, hostkey_len;
        struct string_buf buf;

        if(data_len < 5) {
            ret = _libssh2_error(session, LIBSSH2_ERROR_PROTO,
                                 "Unexpected key length");
            goto clean_exit;
        }

        buf.data = data;
        buf.len = data_len;
        buf.dataptr = buf.data;
        buf.dataptr++; /* advance past packet type */

        if(_libssh2_get_string(&buf, &server_host_key, &hostkey_len)) {
            ret = _libssh2_error(session, LIBSSH2_ERROR_PROTO,
                                 "Unexpected key length");
            goto clean_exit;
        }

        session->server_hostkey_len = (uint32_t)hostkey_len;
        session->server_hostkey = LIBSSH2_ALLOC(session,
                                                session->server_hostkey_len);
        if(!session->server_hostkey) {
            ret = _libssh2_error(session, LIBSSH2_ERROR_ALLOC,
                                 "Unable to allocate memory for a copy "
                                 "of the host key");
            goto clean_exit;
        }

        memcpy(session->server_hostkey, server_host_key,
               session->server_hostkey_len);

#if LIBSSH2_MD5
        {
            libssh2_md5_ctx fingerprint_ctx;

            if(libssh2_md5_init(&fingerprint_ctx)) {
                libssh2_md5_update(fingerprint_ctx, session->server_hostkey,
                                   session->server_hostkey_len);
                libssh2_md5_final(fingerprint_ctx,
                                  session->server_hostkey_md5);
                session->server_hostkey_md5_valid = TRUE;
            }
            else {
                session->server_hostkey_md5_valid = FALSE;
            }
        }
#ifdef LIBSSH2DEBUG
        {
            char fingerprint[50], *fprint = fingerprint;
            int i;
            for(i = 0; i < 16; i++, fprint += 3) {
                snprintf(fprint, 4, "%02x:", session->server_hostkey_md5[i]);
            }
            *(--fprint) = '\0';
            _libssh2_debug(session, LIBSSH2_TRACE_KEX,
                             "Server's MD5 Fingerprint: %s", fingerprint);
        }
#endif /* LIBSSH2DEBUG */
#endif /* ! LIBSSH2_MD5 */

        {
            libssh2_sha1_ctx fingerprint_ctx;

            if(libssh2_sha1_init(&fingerprint_ctx)) {
                libssh2_sha1_update(fingerprint_ctx, session->server_hostkey,
                                    session->server_hostkey_len);
                libssh2_sha1_final(fingerprint_ctx,
                                   session->server_hostkey_sha1);
                session->server_hostkey_sha1_valid = TRUE;
            }
            else {
                session->server_hostkey_sha1_valid = FALSE;
            }
        }
#ifdef LIBSSH2DEBUG
        {
            char fingerprint[64], *fprint = fingerprint;
            int i;

            for(i = 0; i < 20; i++, fprint += 3) {
                snprintf(fprint, 4, "%02x:", session->server_hostkey_sha1[i]);
            }
            *(--fprint) = '\0';
            _libssh2_debug(session, LIBSSH2_TRACE_KEX,
                             "Server's SHA1 Fingerprint: %s", fingerprint);
        }
#endif /* LIBSSH2DEBUG */

        /* SHA256 */
        {
            libssh2_sha256_ctx fingerprint_ctx;

            if(libssh2_sha256_init(&fingerprint_ctx)) {
                libssh2_sha256_update(fingerprint_ctx, session->server_hostkey,
                                      session->server_hostkey_len);
                libssh2_sha256_final(fingerprint_ctx,
                                     session->server_hostkey_sha256);
                session->server_hostkey_sha256_valid = TRUE;
            }
            else {
                session->server_hostkey_sha256_valid = FALSE;
            }
        }
#ifdef LIBSSH2DEBUG
        {
            char *base64Fingerprint = NULL;
            _libssh2_base64_encode(session,
                                   (const char *)
                                   session->server_hostkey_sha256,
                                   SHA256_DIGEST_LENGTH, &base64Fingerprint);
            if(base64Fingerprint != NULL) {
                _libssh2_debug(session, LIBSSH2_TRACE_KEX,
                               "Server's SHA256 Fingerprint: %s",
                               base64Fingerprint);
                LIBSSH2_FREE(session, base64Fingerprint);
            }
        }
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
