charcole/zmachine3270/MAME/SoftDongle/Screen.cpp

#include "Screen.h"
#include "3270.h"
#include <stdio.h>
#include <stdlib.h>
#include <string.h>
#include <unistd.h>
#include <errno.h>

enum
{
    WriteCommand = 0xF1,
    WCC = 0xC3,

    SetBufferAddress = 0x11,
    SetCursor = 0x13,
    RepeatToAddress = 0x3C,

    StartField = 0x1D,
    ProtectedField = 0xF0,
    EditableField = 0x40,
    PasswordField = 0x4C,

    SetAttribute = 0x28,               // Not supported
    FieldAttribute3270 = 0xC0,         // Not supported
    ResetCharacterAttributes = 0x00,   // Not supported
    SetAttributeExtended = 0x29,       // Not supported
    ExtendedHighlightAttribute = 0x41, // Not supported
    HighlightReverseVideo = 0xF2,      // Not supported

    NUL = 0x00
};

Screen GScreen;

Screen::Screen()
{
	Semaphore = sem_open("/screen_semaphore", O_CREAT | O_EXCL, 0, 0);
	if (Semaphore == SEM_FAILED)
	{
		printf("Couldn't create semaphore\n");
		exit(1);
	}
    sem_unlink("/screen_semaphore");

    Clear();
}

void Screen::Clear()
{
    for (int Line = 0; Line < NUM_ROWS; Line++)
    {
        memset(&Row[Line], ' ', sizeof(Row[0]));
    }
    SetCursorPosition(0,0);
}

void Screen::Print(const char *String)
{
    while (String[0])
    {
        Print(String[0]);
        String++;
    }
}

void Screen::Print(char Char)
{
    if (Char < 0x20 || Char >= 0x7F) // Control codes
    {
        if (Char == '\n')
        {
            bWordwrap = false;
            ConditionalScroll();
        }
        return;
    }
    if (bWordwrap)
    {
        bWordwrap = false;
        if (Char == ' ')
        {
            return;
        }
        else
        {
            int LastRow = CursorRow - 1;
            if (LastRow < 0)
            {
                LastRow += NUM_ROWS;
            }
            int LastCol = NUM_COLS - 1;
            int MaxLookback = NUM_COLS / 2;
            while (LastCol > MaxLookback && Row[LastRow].Col[LastCol] != ' ' &&
                   Row[LastRow].Col[LastCol] != ',' && Row[LastRow].Col[LastCol] != '.')
            {
                LastCol--;
            }
            if (LastCol > MaxLookback)
            {
                LastCol++;
                while (LastCol < NUM_COLS)
                {
                    Row[CursorRow].Col[CursorCol++] = Row[LastRow].Col[LastCol];
                    Row[LastRow].Col[LastCol++] = ' ';
                }
            }
            else
            {
                int LastCol = NUM_COLS - 1;
                Row[CursorRow].Col[CursorCol++] = Row[LastRow].Col[LastCol];
                Row[LastRow].Col[LastCol] = '-';
            }
        }
    }
    Row[CursorRow].Col[CursorCol++] = Char;
    if (CursorCol >= NUM_COLS)
    {
        bWordwrap = (Char != ' ');
        ConditionalScroll();
    }
}

int Screen::ReadInput(char* Input, int MaxLength, bool bWantRawInput, int Timeout, bool bPassword, bool bEcho)
{
    ScrollsWithoutInput = 0;
    if (!bSuspended && !bCancelInput)
    {
        WaitingInput = Input;
        bRawInputWanted = bWantRawInput;
        bPasswordInput = bPassword;
        bSuspended = true;
    }
	printf("Trying to read from keybaord (waiting). Timeout:%d\n", Timeout);
	if (Timeout >= 0)
	{
		while (sem_trywait(Semaphore) == EAGAIN)
		{
			usleep(1000);
			Timeout--;
			if (Timeout <= 0)
			{
				return -1;
			}
		}
	}
	else
	{
		sem_wait(Semaphore);
	}
    bCancelInput = false;
    if (LastInputLength < 0) // Successfully cancelled
    {
        return 0;
    }
    if (!bWantRawInput && bEcho)
    {
        Print(' ');
        if (!bPassword)
        {
            Print(Input);
        }
        Print('\n');
        Print('\n');
    }
    return LastInputLength;
}

void Screen::CancelInput()
{
    bCancelInput = true;
}

bool Screen::ShouldCancelInput()
{
    if (bCancelInput)
    {
        LastInputLength = -1;
        bSuspended = false;
		sem_post(Semaphore);
        return true;
    }
    return false;
}

void Screen::AddScreenAddress(char* &Data, int Col, int Row)
{
    uint16_t ScreenAddress = Row * NUM_COLS + Col;
    if (ScreenAddress >= NUM_COLS * NUM_ROWS)
    {
        ScreenAddress -= NUM_COLS * NUM_ROWS;
    }
    ScreenAddress = ((ScreenAddress & 0x0FC0) << 2) | (ScreenAddress & 0x3F);
    ScreenAddress |= 0x4040;
    *(Data++) = ((ScreenAddress >> 8) & 0xFF);
    *(Data++) = (ScreenAddress & 0xFF);
}

void Screen::WriteMultiple(char* &Data, int& Col, int Row, char EBDIC, int Run)
{
    Col += Run;
    if (Run <= 4)
    {
        for (int i = 0; i < Run; i++)
        {
            *(Data++) = EBDIC;
        }
    }
    else
    {
        *(Data++) = RepeatToAddress;
        AddScreenAddress(Data, Col, Row);
        *(Data++) = EBDIC;
    }
}

void Screen::WriteScreenData(char* &Data, int Col, int Row, const char* ASCIIData, int NumData)
{
    int Run = 0;
    char LastChar = 0;
    while (NumData--)
    {
       char EBDIC = ASCIIToEBCDIC[(uint8_t)(*(ASCIIData++))];
       if (EBDIC != LastChar)
       {
           WriteMultiple(Data, Col, Row, LastChar, Run);
           Run = 0;
       }
       LastChar = EBDIC;
       Run++;
    }
    WriteMultiple(Data, Col, Row, LastChar, Run);
}

void Screen::SetRawStream(const char* RawData, int Size)
{
    RawStream = RawData;
    RawStreamSize = Size;
}

int Screen::SerializeScreen3270()
{
    while (!bSuspended)
    {
        usleep(5000);
    }
    
    constexpr int MaxPacketSize = 240;
    int NumPackets = 0;

    if (RawStream)
    {
        // Overrides the screen with raw 3270 datastream. Used for TN3270 support
        Packets[NumPackets].Start = RawStream;
        while (RawStreamSize > 0)
        {
            int Size = RawStreamSize;
            if (Size > MaxPacketSize)
            {
                Size = MaxPacketSize;
            }
            Packets[NumPackets++].Length = Size;
            RawStream += Size;
            RawStreamSize -= Size;
            Packets[NumPackets].Start = RawStream;
        }
        RawStream = nullptr;
        RawStreamSize = 0;
        return NumPackets;
    }

    char* Data = Serialized3270Data;
    
    Packets[NumPackets].Start = Data;

    *(Data++) = WriteCommand;
    *(Data++) = WCC;
    *(Data++) = SetBufferAddress;
    AddScreenAddress(Data, 0, 0);

    char* EndOfPacket = Serialized3270Data + MaxPacketSize;

    int CurrentLine = TopLine;
    for (int Line = 0; Line < NUM_ROWS; Line++)
    {
        char* BeforeLine = Data;
        if (Line == 0)
        {
            *(Data++) = StartField;
            *(Data++) = (char)(ProtectedField + 8);
            WriteScreenData(Data, 1, Line, &Row[CurrentLine].Col[1], sizeof(Row[CurrentLine].Col) - 2);
            *(Data++) = StartField;
            *(Data++) = ProtectedField;
        }
        else
        {
            WriteScreenData(Data, 0, Line, Row[CurrentLine].Col, sizeof(Row[CurrentLine].Col));

            if (CurrentLine == CursorRow)
            {
                *(Data++) = SetBufferAddress;
                AddScreenAddress(Data, CursorCol, Line);
                *(Data++) = StartField;
                *(Data++) = bPasswordInput?PasswordField:EditableField;
                *(Data++) = SetCursor;
                *(Data++) = RepeatToAddress;
                AddScreenAddress(Data, NUM_COLS - 1, Line);
                *(Data++) = NUL;
                *(Data++) = StartField;
                *(Data++) = ProtectedField;
            }
        }
        if (Data > EndOfPacket)
        {
            Packets[NumPackets].Length = BeforeLine - Packets[NumPackets].Start;
            NumPackets++;
            Packets[NumPackets].Start = BeforeLine;
            EndOfPacket = BeforeLine + MaxPacketSize;
        }
        CurrentLine++;
        if (CurrentLine >= NUM_ROWS)
        {
            CurrentLine = 0;
        }
    }
    Packets[NumPackets].Length = Data - Packets[NumPackets].Start;
    NumPackets++;
    return NumPackets;
}

void Screen::Process3270Reply(const uint8_t* Data, int Size)
{
    if (bRawInputWanted)
    {
        memcpy((void *)WaitingInput, Data, Size);
        LastInputLength = Size;
    }
    else
    {
        char InputString[128];
        char *Input = InputString;
        if (Size > 0 && Data[0] == 0x7D) // ENTER key
        {
            int DataOffset = 3;    // Skip AID and cursor address
            if (Size > DataOffset) // Could be it if no input
            {
                if (Data[DataOffset] == 0x11) // Set Buffer Address always seems to follow
                {
                    DataOffset += 3; // SBA + Address
                }
            }

            if (Size - DataOffset < sizeof(InputString) - 1)
            {
                for (int TextIndex = DataOffset; TextIndex < Size; TextIndex++)
                {
                    *(Input++) = EBCDICToASCII[Data[TextIndex]];
                }
            }
        }
        *(Input++) = '\0';
        printf("Input: %s\n", InputString);
        strcpy((char *)WaitingInput, InputString);
        LastInputLength = strlen(InputString);
    }
    bSuspended = false;
	sem_post(Semaphore);
}

void Screen::GetCursorPosition(int& X, int& Y)
{
    X = CursorCol;
    Y = CursorRow - TopLine;
    if (Y < 0)
    {
        Y += NUM_ROWS;
    }
}

void Screen::SetCursorPosition(int X, int Y)
{
    bWordwrap = false;
    CursorCol = X;
    CursorRow = Y + TopLine;
    if (CursorRow >= NUM_ROWS)
    {
        CursorRow -= NUM_ROWS;
    }
}

void Screen::ConditionalScroll()
{
    CursorCol = 0;
    CursorRow++;
    if (CursorRow >= NUM_ROWS)
    {
        CursorRow = 0;
    }
    if (CursorRow == TopLine) // Shift down status line to preserve it
    {
        for (int Line = NonScrollingRows - 1; Line >= 0; Line--)
        {
            memcpy(&Row[(TopLine + 1 + Line) % NUM_ROWS], &Row[(TopLine + Line) % NUM_ROWS], sizeof(Row[0]));
        }
        TopLine = (TopLine + 1) % NUM_ROWS;
        ScrollsWithoutInput++;
    }
    if (ScrollsWithoutInput > NUM_ROWS - NonScrollingRows)
    {
        char Input[128];
        bool bOldWordwrap = bWordwrap;
        bWordwrap = false;
        Print("[MORE]");
        ReadInput(Input, sizeof(Input), false, -1, true, false);
        bWordwrap = bOldWordwrap;
        CursorCol = 0;
    }
    memset(&Row[CursorRow], ' ', sizeof(Row[0]));
}

void ScreenPrint(const char* String)
{
    GScreen.Print(String);
}

void ScreenPrintChar(char Char)
{
    GScreen.Print(Char);
}

void ScreenReadInput(char* Input, int MaxLength)
{
    GScreen.ReadInput(Input, MaxLength);
}

void ScreenReadInputSingle(char* Input, int MaxLength)
{
    GScreen.ReadInput(Input, MaxLength, false, -1, true, false);
}

void ScreenGetCursor(int* CursorX, int* CursorY)
{
    GScreen.GetCursorPosition(*CursorX, *CursorY);
}

void ScreenSetCursor(int CursorX, int CursorY)
{
    GScreen.SetCursorPosition(CursorX, CursorY);
}

void ScreenSetNonScrollRows(int Rows)
{
    GScreen.SetNonScrollingRows(Rows);
}
