charcole/zmachine3270/MAME/SoftDongle/Screen.h

#ifdef __cplusplus
#include <stdint.h>
#include <semaphore.h>

struct Screen
{
public:
    enum
    {
        NUM_ROWS = 24,
        NUM_COLS = 80
    };

    Screen();
    void Clear();
    void Print(const char* String);
    void Print(char Char);
    void GetCursorPosition(int& X, int& Y);
    void SetCursorPosition(int X, int Y);
    void SetNonScrollingRows(int NumRows)
    {
        NonScrollingRows = NumRows;
    }
    
    int ReadInput(char *Input, int MaxLength, bool bWantRawInput = false, int Timeout = -1, bool bPassword = false, bool bEcho = true);
    
    int SerializeScreen3270();
    const char* GetScreen3270Packet(int PacketNum, int& PacketSize)
    {
        PacketSize = Packets[PacketNum].Length;
        return Packets[PacketNum].Start;
    }

    void Process3270Reply(const uint8_t* Data, int Size);
    
    void SetRawStream(const char* RawData, int Size);

    void CancelInput();
    bool ShouldCancelInput();

private:
    void AddScreenAddress(char* &Data, int Col, int Row);
    void WriteMultiple(char* &Data, int& Col, int Row, char EBDIC, int Run);
    void WriteScreenData(char* &Data, int Col, int Row, const char* ASCIIData, int NumData);
    void ConditionalScroll();

    struct FLine
    {
        char Col[NUM_COLS];
    };
    FLine Row[NUM_ROWS];

    struct FPacket
    {
        const char* Start;
        int Length;
    };
    FPacket Packets[NUM_ROWS];

    char Serialized3270Data[NUM_ROWS * (NUM_COLS + 16)]; // Space for header + cursor setting
    
    const char* RawStream = nullptr;
    int RawStreamSize = 0;

    int TopLine = 0;
    int CursorRow = 0;
    int CursorCol = 0;
    int LastInputLength = 0;
    int NonScrollingRows = 1;
    int ScrollsWithoutInput = 0;
    bool bWordwrap = false;
    bool bRawInputWanted = false;
    bool bPasswordInput = false;
    bool bCancelInput = false;
    
    volatile char* WaitingInput = nullptr;
	sem_t* Semaphore;
    volatile bool bSuspended = false;
};

extern Screen GScreen;

extern "C"
{
#endif

void ScreenPrint(const char* String);
void ScreenPrintChar(char Char);
void ScreenReadInput(char* Input, int MaxLength);
void ScreenReadInputSingle(char* Input, int MaxLength);
void ScreenGetCursor(int* CursorX, int* CursorY);
void ScreenSetCursor(int CursorX, int CursorY);
void ScreenSetNonScrollRows(int Rows);

#ifdef __cplusplus
}
#endif
