charcole/zmachine3270/MAME/SoftDongle/Network.h

#pragma once

#include "PacketBuilder.h"
#include "PacketParser.h"

class NetworkState
{
	enum EState
	{
		StateXID,
		StateNrm,
		StateActPU,
		StateActLU,
		StateBind,
		StateDataReset,
		StateSendScreen,
		StateWaitForInput,
		StateRespond,
		StateRespond2
	};

public:
	NetworkState();
	int GenerateNewPackets(uint8_t* Buffer, bool &bWaitForReply);
	void ProcessPacket(const PacketParser& Packet, const uint8_t* Data);

private:
	EState State = StateXID;
	SNAStream Stream;
	uint16_t ProcessedPacket = 0xFFFF;
	int CurrentLine = 0;
	int Num3270Packets = 0;
	int WaitForSequence = -1;
	bool bSendReadyToRecieve = false;
};
